karl-mohring/TrafficCounter/Tests/Test 04 - Lidar (overpass)/Data/Traffic Count - Test 4 - 2015.06.02 1617.xlsx

Sheet: RAW
2015-06-02 | 16:17:47 | 694 | - | INFO | - | Incoming | packet: | {u'count_pir': | 0 | u'lidar_range': | 0 | u'of_dy': | 0 | u'count_uvd': | 0 | u'of_dx': | 0 | u'uvd_range': | 621 | u'count_of': | 0 | u'count_lidar': | 0 | u'version': | 4 | u'of_status': | FALSE | u'pir_status': | FALSE | u'id': | u'trafficCount' | u'of_connected': | FALSE
2015-06-02 | 16:17:56 | 720 | - | INFO | - | Incoming | packet: | {u'count_pir': | 0 | u'lidar_range': | 519 | u'of_dy': | 0 | u'count_uvd': | 1 | u'of_dx': | 0 | u'uvd_range': | 336 | u'count_of': | 0 | u'count_lidar': | 0 | u'version': | 4 | u'of_status': | FALSE | u'pir_status': | FALSE | u'id': | u'trafficCount' | u'of_connected': | TRUE
2015-06-02 | 16:17:59 | 309 | - | INFO | - | Incoming | packet: | {u'count_pir': | 0 | u'lidar_range': | 518 | u'of_dy': | 0 | u'count_uvd': | 2 | u'of_dx': | 0 | u'uvd_range': | 522 | u'count_of': | 0 | u'count_lidar': | 0 | u'version': | 4 | u'of_status': | FALSE | u'pir_status': | FALSE | u'id': | u'trafficCount' | u'of_connected': | TRUE
2015-06-02 | 16:18:06 | 519 | - | INFO | - | Incoming | packet: | {u'count_pir': | 0 | u'lidar_range': | 518 | u'of_dy': | 0 | u'count_uvd': | 3 | u'of_dx': | 0 | u'uvd_range': | 427 | u'count_of': | 0 | u'count_lidar': | 0 | u'version': | 4 | u'of_status': | FALSE | u'pir_status': | FALSE | u'id': | u'trafficCount' | u'of_connected': | TRUE
2015-06-02 | 16:18:12 | 332 | - | INFO | - | Incoming | packet: | {u'count_pir': | 0 | u'lidar_range': | 519 | u'of_dy': | 0 | u'count_uvd': | 4 | u'of_dx': | 0 | u'uvd_range': | 338 | u'count_of': | 0 | u'count_lidar': | 0 | u'version': | 4 | u'of_status': | FALSE | u'pir_status': | FALSE | u'id': | u'trafficCount' | u'of_connected': | TRUE
2015-06-02 | 16:18:14 | 318 | - | INFO | - | Incoming | packet: | {u'count_pir': | 0 | u'lidar_range': | 517 | u'of_dy': | 0 | u'count_uvd': | 5 | u'of_dx': | 0 | u'uvd_range': | 292 | u'count_of': | 0 | u'count_lidar': | 0 | u'version': | 4 | u'of_status': | FALSE | u'pir_status': | FALSE | u'id': | u'trafficCount' | u'of_connected': | TRUE
2015-06-02 | 16:18:14 | 917 | - | INFO | - | Incoming | packet: | {u'count_pir': | 0 | u'lidar_range': | 518 | u'of_dy': | 0 | u'count_uvd': | 6 | u'of_dx': | 0 | u'uvd_range': | 553 | u'count_of': | 0 | u'count_lidar': | 0 | u'version': | 4 | u'of_status': | FALSE | u'pir_status': | FALSE | u'id': | u'trafficCount' | u'of_connected': | TRUE
2015-06-02 | 16:18:16 | 318 | - | INFO | - | Incoming | packet: | {u'count_pir': | 0 | u'lidar_range': | 517 | u'of_dy': | 0 | u'count_uvd': | 7 | u'of_dx': | 0 | u'uvd_range': | 407 | u'count_of': | 0 | u'count_lidar': | 0 | u'version': | 4 | u'of_status': | FALSE | u'pir_status': | FALSE | u'id': | u'trafficCount' | u'of_connected': | TRUE
2015-06-02 | 16:18:18 | 341 | - | INFO | - | Incoming | packet: | {u'count_pir': | 0 | u'lidar_range': | 516 | u'of_dy': | 0 | u'count_uvd': | 8 | u'of_dx': | 0 | u'uvd_range': | 483 | u'count_of': | 0 | u'count_lidar': | 0 | u'version': | 4 | u'of_status': | FALSE | u'pir_status': | FALSE | u'id': | u'trafficCount' | u'of_connected': | TRUE
2015-06-02 | 16:18:18 | 720 | - | INFO | - | Incoming | packet: | {u'count_pir': | 0 | u'lidar_range': | 519 | u'of_dy': | 0 | u'count_uvd': | 9 | u'of_dx': | 0 | u'uvd_range': | 500 | u'count_of': | 0 | u'count_lidar': | 0 | u'version': | 4 | u'of_status': | FALSE | u'pir_status': | FALSE | u'id': | u'trafficCount' | u'of_connected': | TRUE
2015-06-02 | 16:18:24 | 512 | - | INFO | - | Incoming | packet: | {u'count_pir': | 0 | u'lidar_range': | 518 | u'of_dy': | 0 | u'count_uvd': | 10 | u'of_dx': | 0 | u'uvd_range': | 382 | u'count_of': | 0 | u'count_lidar': | 0 | u'version': | 4 | u'of_status': | FALSE | u'pir_status': | FALSE | u'id': | u'trafficCount' | u'of_connected': | TRUE
2015-06-02 | 16:18:27 | 903 | - | INFO | - | Incoming | packet: | {u'count_pir': | 0 | u'lidar_range': | 5 | u'of_dy': | 0 | u'count_uvd': | 10 | u'of_dx': | 0 | u'uvd_range': | 622 | u'count_of': | 0 | u'count_lidar': | 1 | u'version': | 4 | u'of_status': | FALSE | u'pir_status': | FALSE | u'id': | u'trafficCount' | u'of_connected': | TRUE
2015-06-02 | 16:18:28 | 907 | - | INFO | - | Incoming | packet: | {u'count_pir': | 1 | u'lidar_range': | 519 | u'of_dy': | 0 | u'count_uvd': | 10 | u'of_dx': | 0 | u'uvd_range': | 622 | u'count_of': | 0 | u'count_lidar': | 1 | u'version': | 4 | u'of_status': | FALSE | u'pir_status': | FALSE | u'id': | u'trafficCount' | u'of_connected': | TRUE
2015-06-02 | 16:18:30 | 306 | - | INFO | - | Incoming | packet: | {u'count_pir': | 1 | u'lidar_range': | 516 | u'of_dy': | 0 | u'count_uvd': | 11 | u'of_dx': | 0 | u'uvd_range': | 389 | u'count_of': | 0 | u'count_lidar': | 1 | u'version': | 4 | u'of_status': | FALSE | u'pir_status': | TRUE | u'id': | u'trafficCount' | u'of_connected': | TRUE
2015-06-02 | 16:18:34 | 305 | - | INFO | - | Incoming | packet: | {u'count_pir': | 1 | u'lidar_range': | 517 | u'of_dy': | 0 | u'count_uvd': | 12 | u'of_dx': | 0 | u'uvd_range': | 520 | u'count_of': | 0 | u'count_lidar': | 1 | u'version': | 4 | u'of_status': | FALSE | u'pir_status': | TRUE | u'id': | u'trafficCount' | u'of_connected': | TRUE
2015-06-02 | 16:18:36 | 305 | - | INFO | - | Incoming | packet: | {u'count_pir': | 1 | u'lidar_range': | 521 | u'of_dy': | 0 | u'count_uvd': | 13 | u'of_dx': | 0 | u'uvd_range': | 536 | u'count_of': | 0 | u'count_lidar': | 1 | u'version': | 4 | u'of_status': | FALSE | u'pir_status': | FALSE | u'id': | u'trafficCount' | u'of_connected': | TRUE
2015-06-02 | 16:18:38 | 107 | - | INFO | - | Incoming | packet: | {u'count_pir': | 1 | u'lidar_range': | 518 | u'of_dy': | 0 | u'count_uvd': | 14 | u'of_dx': | 0 | u'uvd_range': | 284 | u'count_of': | 0 | u'count_lidar': | 1 | u'version': | 4 | u'of_status': | FALSE | u'pir_status': | FALSE | u'id': | u'trafficCount' | u'of_connected': | TRUE
2015-06-02 | 16:18:42 | 506 | - | INFO | - | Incoming | packet: | {u'count_pir': | 1 | u'lidar_range': | 518 | u'of_dy': | 0 | u'count_uvd': | 15 | u'of_dx': | 0 | u'uvd_range': | 556 | u'count_of': | 0 | u'count_lidar': | 1 | u'version': | 4 | u'of_status': | FALSE | u'pir_status': | FALSE | u'id': | u'trafficCount' | u'of_connected': | TRUE
2015-06-02 | 16:18:42 | 934 | - | INFO | - | Incoming | packet: | {u'count_pir': | 2 | u'lidar_range': | 519 | u'of_dy': | 0 | u'count_uvd': | 15 | u'of_dx': | 0 | u'uvd_range': | 622 | u'count_of': | 0 | u'count_lidar': | 1 | u'version': | 4 | u'of_status': | FALSE | u'pir_status': | FALSE | u'id': | u'trafficCount' | u'of_connected': | TRUE
2015-06-02 | 16:18:53 | 706 | - | INFO | - | Incoming | packet: | {u'count_pir': | 2 | u'lidar_range': | 516 | u'of_dy': | 0 | u'count_uvd': | 16 | u'of_dx': | 0 | u'uvd_range': | 490 | u'count_of': | 0 | u'count_lidar': | 1 | u'version': | 4 | u'of_status': | FALSE | u'pir_status': | FALSE | u'id': | u'trafficCount' | u'of_connected': | TRUE
2015-06-02 | 16:19:04 | 505 | - | INFO | - | Incoming | packet: | {u'count_pir': | 2 | u'lidar_range': | 519 | u'of_dy': | 0 | u'count_uvd': | 17 | u'of_dx': | 0 | u'uvd_range': | 370 | u'count_of': | 0 | u'count_lidar': | 1 | u'version': | 4 | u'of_status': | FALSE | u'pir_status': | FALSE | u'id': | u'trafficCount' | u'of_connected': | TRUE
2015-06-02 | 16:19:14 | 506 | - | INFO | - | Incoming | packet: | {u'count_pir': | 2 | u'lidar_range': | 517 | u'of_dy': | 0 | u'count_uvd': | 18 | u'of_dx': | 0 | u'uvd_range': | 294 | u'count_of': | 0 | u'count_lidar': | 1 | u'version': | 4 | u'of_status': | FALSE | u'pir_status': | FALSE | u'id': | u'trafficCount' | u'of_connected': | TRUE
2015-06-02 | 16:19:18 | 506 | - | INFO | - | Incoming | packet: | {u'count_pir': | 2 | u'lidar_range': | 520 | u'of_dy': | 0 | u'count_uvd': | 19 | u'of_dx': | 0 | u'uvd_range': | 275 | u'count_of': | 0 | u'count_lidar': | 1 | u'version': | 4 | u'of_status': | FALSE | u'pir_status': | FALSE | u'id': | u'trafficCount' | u'of_connected': | TRUE
2015-06-02 | 16:19:18 | 907 | - | INFO | - | Incoming | packet: | {u'count_pir': | 2 | u'lidar_range': | 518 | u'of_dy': | 0 | u'count_uvd': | 20 | u'of_dx': | 0 | u'uvd_range': | 552 | u'count_of': | 0 | u'count_lidar': | 1 | u'version': | 4 | u'of_status': | FALSE | u'pir_status': | FALSE | u'id': | u'trafficCount' | u'of_connected': | TRUE
2015-06-02 | 16:19:20 | 905 | - | INFO | - | Incoming | packet: | {u'count_pir': | 2 | u'lidar_range': | 520 | u'of_dy': | 0 | u'count_uvd': | 21 | u'of_dx': | 0 | u'uvd_range': | 519 | u'count_of': | 0 | u'count_lidar': | 1 | u'version': | 4 | u'of_status': | FALSE | u'pir_status': | FALSE | u'id': | u'trafficCount' | u'of_connected': | TRUE
2015-06-02 | 16:19:29 | 505 | - | INFO | - | Incoming | packet: | {u'count_pir': | 2 | u'lidar_range': | 517 | u'of_dy': | 0 | u'count_uvd': | 22 | u'of_dx': | 0 | u'uvd_range': | 487 | u'count_of': | 0 | u'count_lidar': | 1 | u'version': | 4 | u'of_status': | FALSE | u'pir_status': | FALSE | u'id': | u'trafficCount' | u'of_connected': | TRUE
2015-06-02 | 16:19:30 | 706 | - | INFO | - | Incoming | packet: | {u'count_pir': | 2 | u'lidar_range': | 518 | u'of_dy': | 0 | u'count_uvd': | 23 | u'of_dx': | 0 | u'uvd_range': | 501 | u'count_of': | 0 | u'count_lidar': | 1 | u'version': | 4 | u'of_status': | FALSE | u'pir_status': | FALSE | u'id': | u'trafficCount' | u'of_connected': | TRUE
2015-06-02 | 16:19:32 | 505 | - | INFO | - | Incoming | packet: | {u'count_pir': | 2 | u'lidar_range': | 517 | u'of_dy': | 0 | u'count_uvd': | 24 | u'of_dx': | 0 | u'uvd_range': | 464 | u'count_of': | 0 | u'count_lidar': | 1 | u'version': | 4 | u'of_status': | FALSE | u'pir_status': | FALSE | u'id': | u'trafficCount' | u'of_connected': | TRUE
2015-06-02 | 16:19:33 | 706 | - | INFO | - | Incoming | packet: | {u'count_pir': | 2 | u'lidar_range': | 519 | u'of_dy': | 0 | u'count_uvd': | 25 | u'of_dx': | 0 | u'uvd_range': | 352 | u'count_of': | 0 | u'count_lidar': | 1 | u'version': | 4 | u'of_status': | FALSE | u'pir_status': | FALSE | u'id': | u'trafficCount' | u'of_connected': | TRUE
2015-06-02 | 16:19:36 | 904 | - | INFO | - | Incoming | packet: | {u'count_pir': | 2 | u'lidar_range': | 518 | u'of_dy': | 0 | u'count_uvd': | 26 | u'of_dx': | 0 | u'uvd_range': | 434 | u'count_of': | 0 | u'count_lidar': | 1 | u'version': | 4 | u'of_status': | FALSE | u'pir_status': | FALSE | u'id': | u'trafficCount' | u'of_connected': | TRUE
2015-06-02 | 16:19:39 | 706 | - | INFO | - | Incoming | packet: | {u'count_pir': | 2 | u'lidar_range': | 519 | u'of_dy': | 0 | u'count_uvd': | 27 | u'of_dx': | 0 | u'uvd_range': | 305 | u'count_of': | 0 | u'count_lidar': | 1 | u'version': | 4 | u'of_status': | FALSE | u'pir_status': | FALSE | u'id': | u'trafficCount' | u'of_connected': | TRUE
2015-06-02 | 16:19:46 | 105 | - | INFO | - | Incoming | packet: | {u'count_pir': | 2 | u'lidar_range': | 515 | u'of_dy': | 0 | u'count_uvd': | 28 | u'of_dx': | 0 | u'uvd_range': | 568 | u'count_of': | 0 | u'count_lidar': | 1 | u'version': | 4 | u'of_status': | FALSE | u'pir_status': | FALSE | u'id': | u'trafficCount' | u'of_connected': | TRUE
2015-06-02 | 16:19:48 | 506 | - | INFO | - | Incoming | packet: | {u'count_pir': | 2 | u'lidar_range': | 519 | u'of_dy': | 0 | u'count_uvd': | 29 | u'of_dx': | 0 | u'uvd_range': | 301 | u'count_of': | 0 | u'count_lidar': | 1 | u'version': | 4 | u'of_status': | FALSE | u'pir_status': | FALSE | u'id': | u'trafficCount' | u'of_connected': | TRUE
2015-06-02 | 16:19:48 | 905 | - | INFO | - | Incoming | packet: | {u'count_pir': | 2 | u'lidar_range': | 517 | u'of_dy': | 0 | u'count_uvd': | 30 | u'of_dx': | 0 | u'uvd_range': | 291 | u'count_of': | 0 | u'count_lidar': | 1 | u'version': | 4 | u'of_status': | FALSE | u'pir_status': | FALSE | u'id': | u'trafficCount' | u'of_connected': | TRUE
2015-06-02 | 16:19:49 | 506 | - | INFO | - | Incoming | packet: | {u'count_pir': | 2 | u'lidar_range': | 518 | u'of_dy': | 0 | u'count_uvd': | 31 | u'of_dx': | 0 | u'uvd_range': | 549 | u'count_of': | 0 | u'count_lidar': | 1 | u'version': | 4 | u'of_status': | FALSE | u'pir_status': | FALSE | u'id': | u'trafficCount' | u'of_connected': | TRUE
2015-06-02 | 16:19:57 | 704 | - | INFO | - | Incoming | packet: | {u'count_pir': | 2 | u'lidar_range': | 518 | u'of_dy': | 0 | u'count_uvd': | 32 | u'of_dx': | 0 | u'uvd_range': | 457 | u'count_of': | 0 | u'count_lidar': | 1 | u'version': | 4 | u'of_status': | FALSE | u'pir_status': | FALSE | u'id': | u'trafficCount' | u'of_connected': | TRUE
2015-06-02 | 16:19:58 | 904 | - | INFO | - | Incoming | packet: | {u'count_pir': | 2 | u'lidar_range': | 517 | u'of_dy': | 0 | u'count_uvd': | 33 | u'of_dx': | 0 | u'uvd_range': | 390 | u'count_of': | 0 | u'count_lidar': | 1 | u'version': | 4 | u'of_status': | FALSE | u'pir_status': | FALSE | u'id': | u'trafficCount' | u'of_connected': | TRUE
2015-06-02 | 16:20:05 | 101 | - | INFO | - | Incoming | packet: | {u'count_pir': | 2 | u'lidar_range': | 373 | u'of_dy': | 0 | u'count_uvd': | 33 | u'of_dx': | 0 | u'uvd_range': | 621 | u'count_of': | 0 | u'count_lidar': | 2 | u'version': | 4 | u'of_status': | FALSE | u'pir_status': | FALSE | u'id': | u'trafficCount' | u'of_connected': | TRUE
2015-06-02 | 16:20:05 | 506 | - | INFO | - | Incoming | packet: | {u'count_pir': | 2 | u'lidar_range': | 517 | u'of_dy': | 0 | u'count_uvd': | 34 | u'of_dx': | 0 | u'uvd_range': | 545 | u'count_of': | 0 | u'count_lidar': | 2 | u'version': | 4 | u'of_status': | FALSE | u'pir_status': | FALSE | u'id': | u'trafficCount' | u'of_connected': | TRUE
2015-06-02 | 16:20:07 | 305 | - | INFO | - | Incoming | packet: | {u'count_pir': | 2 | u'lidar_range': | 521 | u'of_dy': | 0 | u'count_uvd': | 35 | u'of_dx': | 0 | u'uvd_range': | 369 | u'count_of': | 0 | u'count_lidar': | 2 | u'version': | 4 | u'of_status': | FALSE | u'pir_status': | FALSE | u'id': | u'trafficCount' | u'of_connected': | TRUE
2015-06-02 | 16:20:08 | 904 | - | INFO | - | Incoming | packet: | {u'count_pir': | 2 | u'lidar_range': | 519 | u'of_dy': | 0 | u'count_uvd': | 36 | u'of_dx': | 0 | u'uvd_range': | 399 | u'count_of': | 0 | u'count_lidar': | 2 | u'version': | 4 | u'of_status': | FALSE | u'pir_status': | FALSE | u'id': | u'trafficCount' | u'of_connected': | TRUE
2015-06-02 | 16:20:11 | 305 | - | INFO | - | Incoming | packet: | {u'count_pir': | 2 | u'lidar_range': | 517 | u'of_dy': | 0 | u'count_uvd': | 37 | u'of_dx': | 0 | u'uvd_range': | 350 | u'count_of': | 0 | u'count_lidar': | 2 | u'version': | 4 | u'of_status': | FALSE | u'pir_status': | FALSE | u'id': | u'trafficCount' | u'of_connected': | TRUE
2015-06-02 | 16:20:22 | 904 | - | INFO | - | Incoming | packet: | {u'count_pir': | 2 | u'lidar_range': | 516 | u'of_dy': | 0 | u'count_uvd': | 38 | u'of_dx': | 0 | u'uvd_range': | 432 | u'count_of': | 0 | u'count_lidar': | 2 | u'version': | 4 | u'of_status': | FALSE | u'pir_status': | FALSE | u'id': | u'trafficCount' | u'of_connected': | TRUE
2015-06-02 | 16:20:27 | 966 | - | INFO | - | Incoming | packet: | {u'count_pir': | 3 | u'lidar_range': | 518 | u'of_dy': | 0 | u'count_uvd': | 38 | u'of_dx': | 0 | u'uvd_range': | 621 | u'count_of': | 0 | u'count_lidar': | 2 | u'version': | 4 | u'of_status': | FALSE | u'pir_status': | FALSE | u'id': | u'trafficCount' | u'of_connected': | TRUE
2015-06-02 | 16:20:30 | 704 | - | INFO | - | Incoming | packet: | {u'count_pir': | 3 | u'lidar_range': | 514 | u'of_dy': | 0 | u'count_uvd': | 39 | u'of_dx': | 0 | u'uvd_range': | 554 | u'count_of': | 0 | u'count_lidar': | 2 | u'version': | 4 | u'of_status': | FALSE | u'pir_status': | TRUE | u'id': | u'trafficCount' | u'of_connected': | TRUE
2015-06-02 | 16:20:39 | 904 | - | INFO | - | Incoming | packet: | {u'count_pir': | 3 | u'lidar_range': | 518 | u'of_dy': | 0 | u'count_uvd': | 40 | u'of_dx': | 0 | u'uvd_range': | 335 | u'count_of': | 0 | u'count_lidar': | 2 | u'version': | 4 | u'of_status': | FALSE | u'pir_status': | FALSE | u'id': | u'trafficCount' | u'of_connected': | TRUE
2015-06-02 | 16:20:46 | 305 | - | INFO | - | Incoming | packet: | {u'count_pir': | 3 | u'lidar_range': | 518 | u'of_dy': | 0 | u'count_uvd': | 41 | u'of_dx': | 0 | u'uvd_range': | 566 | u'count_of': | 0 | u'count_lidar': | 2 | u'version': | 4 | u'of_status': | FALSE | u'pir_status': | FALSE | u'id': | u'trafficCount' | u'of_connected': | TRUE
2015-06-02 | 16:20:48 | 105 | - | INFO | - | Incoming | packet: | {u'count_pir': | 3 | u'lidar_range': | 517 | u'of_dy': | 0 | u'count_uvd': | 42 | u'of_dx': | 0 | u'uvd_range': | 375 | u'count_of': | 0 | u'count_lidar': | 2 | u'version': | 4 | u'of_status': | FALSE | u'pir_status': | FALSE | u'id': | u'trafficCount' | u'of_connected': | TRUE
2015-06-02 | 16:20:57 | 911 | - | INFO | - | Incoming | packet: | {u'count_pir': | 3 | u'lidar_range': | 518 | u'of_dy': | 0 | u'count_uvd': | 43 | u'of_dx': | 0 | u'uvd_range': | 467 | u'count_of': | 0 | u'count_lidar': | 2 | u'version': | 4 | u'of_status': | FALSE | u'pir_status': | FALSE | u'id': | u'trafficCount' | u'of_connected': | TRUE
2015-06-02 | 16:21:01 | 706 | - | INFO | - | Incoming | packet: | {u'count_pir': | 3 | u'lidar_range': | 520 | u'of_dy': | 0 | u'count_uvd': | 44 | u'of_dx': | 0 | u'uvd_range': | 484 | u'count_of': | 0 | u'count_lidar': | 2 | u'version': | 4 | u'of_status': | FALSE | u'pir_status': | FALSE | u'id': | u'trafficCount' | u'of_connected': | TRUE
2015-06-02 | 16:21:07 | 506 | - | INFO | - | Incoming | packet: | {u'count_pir': | 3 | u'lidar_range': | 519 | u'of_dy': | 0 | u'count_uvd': | 45 | u'of_dx': | 0 | u'uvd_range': | 502 | u'count_of': | 0 | u'count_lidar': | 2 | u'version': | 4 | u'of_status': | FALSE | u'pir_status': | FALSE | u'id': | u'trafficCount' | u'of_connected': | TRUE
2015-06-02 | 16:21:10 | 915 | - | INFO | - | Incoming | packet: | {u'count_pir': | 3 | u'lidar_range': | 518 | u'of_dy': | 0 | u'count_uvd': | 46 | u'of_dx': | 0 | u'uvd_range': | 332 | u'count_of': | 0 | u'count_lidar': | 2 | u'version': | 4 | u'of_status': | FALSE | u'pir_status': | FALSE | u'id': | u'trafficCount' | u'of_connected': | TRUE
2015-06-02 | 16:21:13 | 312 | - | INFO | - | Incoming | packet: | {u'count_pir': | 3 | u'lidar_range': | 519 | u'of_dy': | 0 | u'count_uvd': | 47 | u'of_dx': | 0 | u'uvd_range': | 495 | u'count_of': | 0 | u'count_lidar': | 2 | u'version': | 4 | u'of_status': | FALSE | u'pir_status': | FALSE | u'id': | u'trafficCount' | u'of_connected': | TRUE
2015-06-02 | 16:21:18 | 302 | - | INFO | - | Incoming | packet: | {u'count_pir': | 3 | u'lidar_range': | 369 | u'of_dy': | 0 | u'count_uvd': | 47 | u'of_dx': | 0 | u'uvd_range': | 622 | u'count_of': | 0 | u'count_lidar': | 3 | u'version': | 4 | u'of_status': | FALSE | u'pir_status': | FALSE | u'id': | u'trafficCount' | u'of_connected': | TRUE
2015-06-02 | 16:21:19 | 706 | - | INFO | - | Incoming | packet: | {u'count_pir': | 3 | u'lidar_range': | 516 | u'of_dy': | 0 | u'count_uvd': | 48 | u'of_dx': | 0 | u'uvd_range': | 444 | u'count_of': | 0 | u'count_lidar': | 3 | u'version': | 4 | u'of_status': | FALSE | u'pir_status': | FALSE | u'id': | u'trafficCount' | u'of_connected': | TRUE
2015-06-02 | 16:21:20 | 305 | - | INFO | - | Incoming | packet: | {u'count_pir': | 3 | u'lidar_range': | 518 | u'of_dy': | 0 | u'count_uvd': | 49 | u'of_dx': | 0 | u'uvd_range': | 553 | u'count_of': | 0 | u'count_lidar': | 3 | u'version': | 4 | u'of_status': | FALSE | u'pir_status': | FALSE | u'id': | u'trafficCount' | u'of_connected': | TRUE
2015-06-02 | 16:21:22 | 506 | - | INFO | - | Incoming | packet: | {u'count_pir': | 3 | u'lidar_range': | 514 | u'of_dy': | 0 | u'count_uvd': | 50 | u'of_dx': | 0 | u'uvd_range': | 266 | u'count_of': | 0 | u'count_lidar': | 3 | u'version': | 4 | u'of_status': | FALSE | u'pir_status': | FALSE | u'id': | u'trafficCount' | u'of_connected': | TRUE
2015-06-02 | 16:21:26 | 505 | - | INFO | - | Incoming | packet: | {u'count_pir': | 3 | u'lidar_range': | 517 | u'of_dy': | 0 | u'count_uvd': | 51 | u'of_dx': | 0 | u'uvd_range': | 404 | u'count_of': | 0 | u'count_lidar': | 3 | u'version': | 4 | u'of_status': | FALSE | u'pir_status': | FALSE | u'id': | u'trafficCount' | u'of_connected': | TRUE
2015-06-02 | 16:21:27 | 701 | - | INFO | - | Incoming | packet: | {u'count_pir': | 3 | u'lidar_range': | 418 | u'of_dy': | 0 | u'count_uvd': | 51 | u'of_dx': | 0 | u'uvd_range': | 622 | u'count_of': | 0 | u'count_lidar': | 4 | u'version': | 4 | u'of_status': | FALSE | u'pir_status': | FALSE | u'id': | u'trafficCount' | u'of_connected': | TRUE
2015-06-02 | 16:21:28 | 904 | - | INFO | - | Incoming | packet: | {u'count_pir': | 3 | u'lidar_range': | 519 | u'of_dy': | 0 | u'count_uvd': | 52 | u'of_dx': | 0 | u'uvd_range': | 513 | u'count_of': | 0 | u'count_lidar': | 4 | u'version': | 4 | u'of_status': | FALSE | u'pir_status': | FALSE | u'id': | u'trafficCount' | u'of_connected': | TRUE
2015-06-02 | 16:21:30 | 305 | - | INFO | - | Incoming | packet: | {u'count_pir': | 3 | u'lidar_range': | 519 | u'of_dy': | 0 | u'count_uvd': | 53 | u'of_dx': | 0 | u'uvd_range': | 380 | u'count_of': | 0 | u'count_lidar': | 4 | u'version': | 4 | u'of_status': | FALSE | u'pir_status': | FALSE | u'id': | u'trafficCount' | u'of_connected': | TRUE
2015-06-02 | 16:21:32 | 707 | - | INFO | - | Incoming | packet: | {u'count_pir': | 3 | u'lidar_range': | 521 | u'of_dy': | 0 | u'count_uvd': | 54 | u'of_dx': | 0 | u'uvd_range': | 480 | u'count_of': | 0 | u'count_lidar': | 4 | u'version': | 4 | u'of_status': | FALSE | u'pir_status': | FALSE | u'id': | u'trafficCount' | u'of_connected': | TRUE
2015-06-02 | 16:21:36 | 105 | - | INFO | - | Incoming | packet: | {u'count_pir': | 3 | u'lidar_range': | 518 | u'of_dy': | 0 | u'count_uvd': | 55 | u'of_dx': | 0 | u'uvd_range': | 362 | u'count_of': | 0 | u'count_lidar': | 4 | u'version': | 4 | u'of_status': | FALSE | u'pir_status': | FALSE | u'id': | u'trafficCount' | u'of_connected': | TRUE
2015-06-02 | 16:21:41 | 904 | - | INFO | - | Incoming | packet: | {u'count_pir': | 3 | u'lidar_range': | 518 | u'of_dy': | 0 | u'count_uvd': | 56 | u'of_dx': | 0 | u'uvd_range': | 331 | u'count_of': | 0 | u'count_lidar': | 4 | u'version': | 4 | u'of_status': | FALSE | u'pir_status': | FALSE | u'id': | u'trafficCount' | u'of_connected': | TRUE
2015-06-02 | 16:21:43 | 904 | - | INFO | - | Incoming | packet: | {u'count_pir': | 3 | u'lidar_range': | 519 | u'of_dy': | 0 | u'count_uvd': | 57 | u'of_dx': | 0 | u'uvd_range': | 422 | u'count_of': | 0 | u'count_lidar': | 4 | u'version': | 4 | u'of_status': | FALSE | u'pir_status': | FALSE | u'id': | u'trafficCount' | u'of_connected': | TRUE
2015-06-02 | 16:21:44 | 500 | - | INFO | - | Incoming | packet: | {u'count_pir': | 3 | u'lidar_range': | 341 | u'of_dy': | 0 | u'count_uvd': | 57 | u'of_dx': | 0 | u'uvd_range': | 621 | u'count_of': | 0 | u'count_lidar': | 5 | u'version': | 4 | u'of_status': | FALSE | u'pir_status': | FALSE | u'id': | u'trafficCount' | u'of_connected': | TRUE
2015-06-02 | 16:21:45 | 303 | - | INFO | - | Incoming | packet: | {u'count_pir': | 3 | u'lidar_range': | 519 | u'of_dy': | 0 | u'count_uvd': | 58 | u'of_dx': | 0 | u'uvd_range': | 334 | u'count_of': | 0 | u'count_lidar': | 5 | u'version': | 4 | u'of_status': | FALSE | u'pir_status': | FALSE | u'id': | u'trafficCount' | u'of_connected': | TRUE
2015-06-02 | 16:21:46 | 99 | - | INFO | - | Incoming | packet: | {u'count_pir': | 3 | u'lidar_range': | 413 | u'of_dy': | 0 | u'count_uvd': | 58 | u'of_dx': | 0 | u'uvd_range': | 622 | u'count_of': | 0 | u'count_lidar': | 6 | u'version': | 4 | u'of_status': | FALSE | u'pir_status': | FALSE | u'id': | u'trafficCount' | u'of_connected': | TRUE
2015-06-02 | 16:21:47 | 704 | - | INFO | - | Incoming | packet: | {u'count_pir': | 3 | u'lidar_range': | 490 | u'of_dy': | 0 | u'count_uvd': | 59 | u'of_dx': | 0 | u'uvd_range': | 298 | u'count_of': | 0 | u'count_lidar': | 6 | u'version': | 4 | u'of_status': | FALSE | u'pir_status': | FALSE | u'id': | u'trafficCount' | u'of_connected': | TRUE
2015-06-02 | 16:21:48 | 500 | - | INFO | - | Incoming | packet: | {u'count_pir': | 3 | u'lidar_range': | 402 | u'of_dy': | 0 | u'count_uvd': | 59 | u'of_dx': | 0 | u'uvd_range': | 585 | u'count_of': | 0 | u'count_lidar': | 7 | u'version': | 4 | u'of_status': | FALSE | u'pir_status': | FALSE | u'id': | u'trafficCount' | u'of_connected': | TRUE
2015-06-02 | 16:21:50 | 305 | - | INFO | - | Incoming | packet: | {u'count_pir': | 3 | u'lidar_range': | 520 | u'of_dy': | 0 | u'count_uvd': | 60 | u'of_dx': | 0 | u'uvd_range': | 570 | u'count_of': | 0 | u'count_lidar': | 7 | u'version': | 4 | u'of_status': | FALSE | u'pir_status': | FALSE | u'id': | u'trafficCount' | u'of_connected': | TRUE
2015-06-02 | 16:21:51 | 503 | - | INFO | - | Incoming | packet: | {u'count_pir': | 3 | u'lidar_range': | 517 | u'of_dy': | 0 | u'count_uvd': | 61 | u'of_dx': | 0 | u'uvd_range': | 331 | u'count_of': | 0 | u'count_lidar': | 7 | u'version': | 4 | u'of_status': | FALSE | u'pir_status': | FALSE | u'id': | u'trafficCount' | u'of_connected': | TRUE
2015-06-02 | 16:21:55 | 901 | - | INFO | - | Incoming | packet: | {u'count_pir': | 3 | u'lidar_range': | 353 | u'of_dy': | 0 | u'count_uvd': | 61 | u'of_dx': | 0 | u'uvd_range': | 622 | u'count_of': | 0 | u'count_lidar': | 8 | u'version': | 4 | u'of_status': | FALSE | u'pir_status': | FALSE | u'id': | u'trafficCount' | u'of_connected': | TRUE
2015-06-02 | 16:21:57 | 303 | - | INFO | - | Incoming | packet: | {u'count_pir': | 3 | u'lidar_range': | 518 | u'of_dy': | 0 | u'count_uvd': | 62 | u'of_dx': | 0 | u'uvd_range': | 311 | u'count_of': | 0 | u'count_lidar': | 8 | u'version': | 4 | u'of_status': | FALSE | u'pir_status': | FALSE | u'id': | u'trafficCount' | u'of_connected': | TRUE
2015-06-02 | 16:21:57 | 500 | - | INFO | - | Incoming | packet: | {u'count_pir': | 3 | u'lidar_range': | 454 | u'of_dy': | 0 | u'count_uvd': | 62 | u'of_dx': | 0 | u'uvd_range': | 311 | u'count_of': | 0 | u'count_lidar': | 9 | u'version': | 4 | u'of_status': | FALSE | u'pir_status': | FALSE | u'id': | u'trafficCount' | u'of_connected': | TRUE
2015-06-02 | 16:21:58 | 503 | - | INFO | - | Incoming | packet: | {u'count_pir': | 3 | u'lidar_range': | 383 | u'of_dy': | 0 | u'count_uvd': | 62 | u'of_dx': | 0 | u'uvd_range': | 621 | u'count_of': | 0 | u'count_lidar': | 10 | u'version': | 4 | u'of_status': | FALSE | u'pir_status': | FALSE | u'id': | u'trafficCount' | u'of_connected': | TRUE
2015-06-02 | 16:22:07 | 105 | - | INFO | - | Incoming | packet: | {u'count_pir': | 3 | u'lidar_range': | 516 | u'of_dy': | 0 | u'count_uvd': | 63 | u'of_dx': | 0 | u'uvd_range': | 431 | u'count_of': | 0 | u'count_lidar': | 10 | u'version': | 4 | u'of_status': | FALSE | u'pir_status': | FALSE | u'id': | u'trafficCount' | u'of_connected': | TRUE
2015-06-02 | 16:22:10 | 0 | - | INFO | - | Incoming | packet: | {u'count_pir': | 4 | u'lidar_range': | 516 | u'of_dy': | 0 | u'count_uvd': | 63 | u'of_dx': | 0 | u'uvd_range': | 622 | u'count_of': | 0 | u'count_lidar': | 10 | u'version': | 4 | u'of_status': | FALSE | u'pir_status': | FALSE | u'id': | u'trafficCount' | u'of_connected': | TRUE
2015-06-02 | 16:22:15 | 104 | - | INFO | - | Incoming | packet: | {u'count_pir': | 4 | u'lidar_range': | 448 | u'of_dy': | 0 | u'count_uvd': | 63 | u'of_dx': | 0 | u'uvd_range': | 622 | u'count_of': | 0 | u'count_lidar': | 11 | u'version': | 4 | u'of_status': | FALSE | u'pir_status': | TRUE | u'id': | u'trafficCount' | u'of_connected': | TRUE
2015-06-02 | 16:22:15 | 302 | - | INFO | - | Incoming | packet: | {u'count_pir': | 4 | u'lidar_range': | 343 | u'of_dy': | 0 | u'count_uvd': | 63 | u'of_dx': | 0 | u'uvd_range': | 621 | u'count_of': | 0 | u'count_lidar': | 12 | u'version': | 4 | u'of_status': | FALSE | u'pir_status': | TRUE | u'id': | u'trafficCount' | u'of_connected': | TRUE
2015-06-02 | 16:22:16 | 305 | - | INFO | - | Incoming | packet: | {u'count_pir': | 4 | u'lidar_range': | 401 | u'of_dy': | 0 | u'count_uvd': | 64 | u'of_dx': | 0 | u'uvd_range': | 290 | u'count_of': | 0 | u'count_lidar': | 12 | u'version': | 4 | u'of_status': | FALSE | u'pir_status': | FALSE | u'id': | u'trafficCount' | u'of_connected': | TRUE
2015-06-02 | 16:22:18 | 704 | - | INFO | - | Incoming | packet: | {u'count_pir': | 4 | u'lidar_range': | 373 | u'of_dy': | 0 | u'count_uvd': | 65 | u'of_dx': | 0 | u'uvd_range': | 401 | u'count_of': | 0 | u'count_lidar': | 12 | u'version': | 4 | u'of_status': | FALSE | u'pir_status': | FALSE | u'id': | u'trafficCount' | u'of_connected': | TRUE
2015-06-02 | 16:22:21 | 703 | - | INFO | - | Incoming | packet: | {u'count_pir': | 4 | u'lidar_range': | 517 | u'of_dy': | 0 | u'count_uvd': | 66 | u'of_dx': | 0 | u'uvd_range': | 429 | u'count_of': | 0 | u'count_lidar': | 12 | u'version': | 4 | u'of_status': | FALSE | u'pir_status': | FALSE | u'id': | u'trafficCount' | u'of_connected': | TRUE
2015-06-02 | 16:22:22 | 704 | - | INFO | - | Incoming | packet: | {u'count_pir': | 4 | u'lidar_range': | 516 | u'of_dy': | 0 | u'count_uvd': | 67 | u'of_dx': | 0 | u'uvd_range': | 513 | u'count_of': | 0 | u'count_lidar': | 12 | u'version': | 4 | u'of_status': | FALSE | u'pir_status': | FALSE | u'id': | u'trafficCount' | u'of_connected': | TRUE
2015-06-02 | 16:22:28 | 505 | - | INFO | - | Incoming | packet: | {u'count_pir': | 4 | u'lidar_range': | 518 | u'of_dy': | 0 | u'count_uvd': | 68 | u'of_dx': | 0 | u'uvd_range': | 475 | u'count_of': | 0 | u'count_lidar': | 12 | u'version': | 4 | u'of_status': | FALSE | u'pir_status': | FALSE | u'id': | u'trafficCount' | u'of_connected': | TRUE
2015-06-02 | 16:22:31 | 904 | - | INFO | - | Incoming | packet: | {u'count_pir': | 4 | u'lidar_range': | 518 | u'of_dy': | 0 | u'count_uvd': | 69 | u'of_dx': | 0 | u'uvd_range': | 384 | u'count_of': | 0 | u'count_lidar': | 12 | u'version': | 4 | u'of_status': | FALSE | u'pir_status': | FALSE | u'id': | u'trafficCount' | u'of_connected': | TRUE
2015-06-02 | 16:22:35 | 704 | - | INFO | - | Incoming | packet: | {u'count_pir': | 4 | u'lidar_range': | 521 | u'of_dy': | 0 | u'count_uvd': | 70 | u'of_dx': | 0 | u'uvd_range': | 273 | u'count_of': | 0 | u'count_lidar': | 12 | u'version': | 4 | u'of_status': | FALSE | u'pir_status': | FALSE | u'id': | u'trafficCount' | u'of_connected': | TRUE
2015-06-02 | 16:22:38 | 305 | - | INFO | - | Incoming | packet: | {u'count_pir': | 4 | u'lidar_range': | 517 | u'of_dy': | 0 | u'count_uvd': | 71 | u'of_dx': | 0 | u'uvd_range': | 542 | u'count_of': | 0 | u'count_lidar': | 12 | u'version': | 4 | u'of_status': | FALSE | u'pir_status': | FALSE | u'id': | u'trafficCount' | u'of_connected': | TRUE
2015-06-02 | 16:22:49 | 703 | - | INFO | - | Incoming | packet: | {u'count_pir': | 4 | u'lidar_range': | 518 | u'of_dy': | 0 | u'count_uvd': | 72 | u'of_dx': | 0 | u'uvd_range': | 323 | u'count_of': | 0 | u'count_lidar': | 12 | u'version': | 4 | u'of_status': | FALSE | u'pir_status': | FALSE | u'id': | u'trafficCount' | u'of_connected': | TRUE
2015-06-02 | 16:22:51 | 305 | - | INFO | - | Incoming | packet: | {u'count_pir': | 4 | u'lidar_range': | 518 | u'of_dy': | 0 | u'count_uvd': | 73 | u'of_dx': | 0 | u'uvd_range': | 346 | u'count_of': | 0 | u'count_lidar': | 12 | u'version': | 4 | u'of_status': | FALSE | u'pir_status': | FALSE | u'id': | u'trafficCount' | u'of_connected': | TRUE
2015-06-02 | 16:22:53 | 704 | - | INFO | - | Incoming | packet: | {u'count_pir': | 4 | u'lidar_range': | 515 | u'of_dy': | 0 | u'count_uvd': | 74 | u'of_dx': | 0 | u'uvd_range': | 475 | u'count_of': | 0 | u'count_lidar': | 12 | u'version': | 4 | u'of_status': | FALSE | u'pir_status': | FALSE | u'id': | u'trafficCount' | u'of_connected': | TRUE
2015-06-02 | 16:22:59 | 905 | - | INFO | - | Incoming | packet: | {u'count_pir': | 4 | u'lidar_range': | 516 | u'of_dy': | 0 | u'count_uvd': | 75 | u'of_dx': | 0 | u'uvd_range': | 491 | u'count_of': | 0 | u'count_lidar': | 12 | u'version': | 4 | u'of_status': | FALSE | u'pir_status': | FALSE | u'id': | u'trafficCount' | u'of_connected': | TRUE
2015-06-02 | 16:23:16 | 505 | - | INFO | - | Incoming | packet: | {u'count_pir': | 4 | u'lidar_range': | 517 | u'of_dy': | 0 | u'count_uvd': | 76 | u'of_dx': | 0 | u'uvd_range': | 376 | u'count_of': | 0 | u'count_lidar': | 12 | u'version': | 4 | u'of_status': | FALSE | u'pir_status': | FALSE | u'id': | u'trafficCount' | u'of_connected': | TRUE
2015-06-02 | 16:23:20 | 904 | - | INFO | - | Incoming | packet: | {u'count_pir': | 4 | u'lidar_range': | 517 | u'of_dy': | 0 | u'count_uvd': | 77 | u'of_dx': | 0 | u'uvd_range': | 538 | u'count_of': | 0 | u'count_lidar': | 12 | u'version': | 4 | u'of_status': | FALSE | u'pir_status': | FALSE | u'id': | u'trafficCount' | u'of_connected': | TRUE
2015-06-02 | 16:23:30 | 505 | - | INFO | - | Incoming | packet: | {u'count_pir': | 4 | u'lidar_range': | 519 | u'of_dy': | 0 | u'count_uvd': | 78 | u'of_dx': | 0 | u'uvd_range': | 559 | u'count_of': | 0 | u'count_lidar': | 12 | u'version': | 4 | u'of_status': | FALSE | u'pir_status': | FALSE | u'id': | u'trafficCount' | u'of_connected': | TRUE
2015-06-02 | 16:23:31 | 505 | - | INFO | - | Incoming | packet: | {u'count_pir': | 4 | u'lidar_range': | 515 | u'of_dy': | 0 | u'count_uvd': | 79 | u'of_dx': | 0 | u'uvd_range': | 557 | u'count_of': | 0 | u'count_lidar': | 12 | u'version': | 4 | u'of_status': | FALSE | u'pir_status': | FALSE | u'id': | u'trafficCount' | u'of_connected': | TRUE
2015-06-02 | 16:23:33 | 904 | - | INFO | - | Incoming | packet: | {u'count_pir': | 4 | u'lidar_range': | 516 | u'of_dy': | 0 | u'count_uvd': | 80 | u'of_dx': | 0 | u'uvd_range': | 289 | u'count_of': | 0 | u'count_lidar': | 12 | u'version': | 4 | u'of_status': | FALSE | u'pir_status': | FALSE | u'id': | u'trafficCount' | u'of_connected': | TRUE
2015-06-02 | 16:23:36 | 703 | - | INFO | - | Incoming | packet: | {u'count_pir': | 4 | u'lidar_range': | 521 | u'of_dy': | 0 | u'count_uvd': | 81 | u'of_dx': | 0 | u'uvd_range': | 321 | u'count_of': | 0 | u'count_lidar': | 12 | u'version': | 4 | u'of_status': | FALSE | u'pir_status': | FALSE | u'id': | u'trafficCount' | u'of_connected': | TRUE
2015-06-02 | 16:23:37 | 704 | - | INFO | - | Incoming | packet: | {u'count_pir': | 4 | u'lidar_range': | 518 | u'of_dy': | 0 | u'count_uvd': | 82 | u'of_dx': | 0 | u'uvd_range': | 312 | u'count_of': | 0 | u'count_lidar': | 12 | u'version': | 4 | u'of_status': | FALSE | u'pir_status': | FALSE | u'id': | u'trafficCount' | u'of_connected': | TRUE
2015-06-02 | 16:23:41 | 703 | - | INFO | - | Incoming | packet: | {u'count_pir': | 4 | u'lidar_range': | 518 | u'of_dy': | 0 | u'count_uvd': | 83 | u'of_dx': | 0 | u'uvd_range': | 454 | u'count_of': | 0 | u'count_lidar': | 12 | u'version': | 4 | u'of_status': | FALSE | u'pir_status': | FALSE | u'id': | u'trafficCount' | u'of_connected': | TRUE
2015-06-02 | 16:23:46 | 105 | - | INFO | - | Incoming | packet: | {u'count_pir': | 4 | u'lidar_range': | 517 | u'of_dy': | 0 | u'count_uvd': | 84 | u'of_dx': | 0 | u'uvd_range': | 533 | u'count_of': | 0 | u'count_lidar': | 12 | u'version': | 4 | u'of_status': | FALSE | u'pir_status': | FALSE | u'id': | u'trafficCount' | u'of_connected': | TRUE
2015-06-02 | 16:23:49 | 904 | - | INFO | - | Incoming | packet: | {u'count_pir': | 4 | u'lidar_range': | 517 | u'of_dy': | 0 | u'count_uvd': | 85 | u'of_dx': | 0 | u'uvd_range': | 558 | u'count_of': | 0 | u'count_lidar': | 12 | u'version': | 4 | u'of_status': | FALSE | u'pir_status': | FALSE | u'id': | u'trafficCount' | u'of_connected': | TRUE
2015-06-02 | 16:23:56 | 904 | - | INFO | - | Incoming | packet: | {u'count_pir': | 4 | u'lidar_range': | 519 | u'of_dy': | 0 | u'count_uvd': | 86 | u'of_dx': | 0 | u'uvd_range': | 442 | u'count_of': | 0 | u'count_lidar': | 12 | u'version': | 4 | u'of_status': | FALSE | u'pir_status': | FALSE | u'id': | u'trafficCount' | u'of_connected': | TRUE
2015-06-02 | 16:23:58 | 901 | - | INFO | - | Incoming | packet: | {u'count_pir': | 4 | u'lidar_range': | 391 | u'of_dy': | 0 | u'count_uvd': | 86 | u'of_dx': | 0 | u'uvd_range': | 621 | u'count_of': | 0 | u'count_lidar': | 13 | u'version': | 4 | u'of_status': | FALSE | u'pir_status': | FALSE | u'id': | u'trafficCount' | u'of_connected': | TRUE
2015-06-02 | 16:24:01 | 900 | - | INFO | - | Incoming | packet: | {u'count_pir': | 4 | u'lidar_range': | 432 | u'of_dy': | 0 | u'count_uvd': | 86 | u'of_dx': | 0 | u'uvd_range': | 621 | u'count_of': | 0 | u'count_lidar': | 14 | u'version': | 4 | u'of_status': | FALSE | u'pir_status': | FALSE | u'id': | u'trafficCount' | u'of_connected': | TRUE
2015-06-02 | 16:24:08 | 303 | - | INFO | - | Incoming | packet: | {u'count_pir': | 4 | u'lidar_range': | 520 | u'of_dy': | 0 | u'count_uvd': | 87 | u'of_dx': | 0 | u'uvd_range': | 335 | u'count_of': | 0 | u'count_lidar': | 14 | u'version': | 4 | u'of_status': | FALSE | u'pir_status': | FALSE | u'id': | u'trafficCount' | u'of_connected': | TRUE
2015-06-02 | 16:24:08 | 703 | - | INFO | - | Incoming | packet: | {u'count_pir': | 4 | u'lidar_range': | 506 | u'of_dy': | 0 | u'count_uvd': | 88 | u'of_dx': | 0 | u'uvd_range': | 302 | u'count_of': | 0 | u'count_lidar': | 14 | u'version': | 4 | u'of_status': | FALSE | u'pir_status': | FALSE | u'id': | u'trafficCount' | u'of_connected': | TRUE
2015-06-02 | 16:24:09 | 301 | - | INFO | - | Incoming | packet: | {u'count_pir': | 4 | u'lidar_range': | 391 | u'of_dy': | 0 | u'count_uvd': | 88 | u'of_dx': | 0 | u'uvd_range': | 622 | u'count_of': | 0 | u'count_lidar': | 15 | u'version': | 4 | u'of_status': | FALSE | u'pir_status': | FALSE | u'id': | u'trafficCount' | u'of_connected': | TRUE
2015-06-02 | 16:24:10 | 901 | - | INFO | - | Incoming | packet: | {u'count_pir': | 4 | u'lidar_range': | 390 | u'of_dy': | 0 | u'count_uvd': | 88 | u'of_dx': | 0 | u'uvd_range': | 621 | u'count_of': | 0 | u'count_lidar': | 16 | u'version': | 4 | u'of_status': | FALSE | u'pir_status': | FALSE | u'id': | u'trafficCount' | u'of_connected': | TRUE
2015-06-02 | 16:24:12 | 104 | - | INFO | - | Incoming | packet: | {u'count_pir': | 4 | u'lidar_range': | 412 | u'of_dy': | 0 | u'count_uvd': | 89 | u'of_dx': | 0 | u'uvd_range': | 301 | u'count_of': | 0 | u'count_lidar': | 16 | u'version': | 4 | u'of_status': | FALSE | u'pir_status': | FALSE | u'id': | u'trafficCount' | u'of_connected': | TRUE
2015-06-02 | 16:24:14 | 104 | - | INFO | - | Incoming | packet: | {u'count_pir': | 4 | u'lidar_range': | 518 | u'of_dy': | 0 | u'count_uvd': | 90 | u'of_dx': | 0 | u'uvd_range': | 291 | u'count_of': | 0 | u'count_lidar': | 16 | u'version': | 4 | u'of_status': | FALSE | u'pir_status': | FALSE | u'id': | u'trafficCount' | u'of_connected': | TRUE
2015-06-02 | 16:24:22 | 503 | - | INFO | - | Incoming | packet: | {u'count_pir': | 4 | u'lidar_range': | 519 | u'of_dy': | 0 | u'count_uvd': | 91 | u'of_dx': | 0 | u'uvd_range': | 347 | u'count_of': | 0 | u'count_lidar': | 16 | u'version': | 4 | u'of_status': | FALSE | u'pir_status': | FALSE | u'id': | u'trafficCount' | u'of_connected': | TRUE
2015-06-02 | 16:24:23 | 701 | - | INFO | - | Incoming | packet: | {u'count_pir': | 4 | u'lidar_range': | 368 | u'of_dy': | 0 | u'count_uvd': | 91 | u'of_dx': | 0 | u'uvd_range': | 622 | u'count_of': | 0 | u'count_lidar': | 17 | u'version': | 4 | u'of_status': | FALSE | u'pir_status': | FALSE | u'id': | u'trafficCount' | u'of_connected': | TRUE
2015-06-02 | 16:24:27 | 703 | - | INFO | - | Incoming | packet: | {u'count_pir': | 4 | u'lidar_range': | 515 | u'of_dy': | 0 | u'count_uvd': | 92 | u'of_dx': | 0 | u'uvd_range': | 312 | u'count_of': | 0 | u'count_lidar': | 17 | u'version': | 4 | u'of_status': | FALSE | u'pir_status': | FALSE | u'id': | u'trafficCount' | u'of_connected': | TRUE
2015-06-02 | 16:24:30 | 104 | - | INFO | - | Incoming | packet: | {u'count_pir': | 4 | u'lidar_range': | 518 | u'of_dy': | 0 | u'count_uvd': | 93 | u'of_dx': | 0 | u'uvd_range': | 461 | u'count_of': | 0 | u'count_lidar': | 17 | u'version': | 4 | u'of_status': | FALSE | u'pir_status': | FALSE | u'id': | u'trafficCount' | u'of_connected': | TRUE
2015-06-02 | 16:24:37 | 303 | - | INFO | - | Incoming | packet: | {u'count_pir': | 4 | u'lidar_range': | 516 | u'of_dy': | 0 | u'count_uvd': | 94 | u'of_dx': | 0 | u'uvd_range': | 317 | u'count_of': | 0 | u'count_lidar': | 17 | u'version': | 4 | u'of_status': | FALSE | u'pir_status': | FALSE | u'id': | u'trafficCount' | u'of_connected': | TRUE
2015-06-02 | 16:24:39 | 303 | - | INFO | - | Incoming | packet: | {u'count_pir': | 4 | u'lidar_range': | 517 | u'of_dy': | 0 | u'count_uvd': | 95 | u'of_dx': | 0 | u'uvd_range': | 272 | u'count_of': | 0 | u'count_lidar': | 17 | u'version': | 4 | u'of_status': | FALSE | u'pir_status': | FALSE | u'id': | u'trafficCount' | u'of_connected': | TRUE
2015-06-02 | 16:24:39 | 903 | - | INFO | - | Incoming | packet: | {u'count_pir': | 4 | u'lidar_range': | 519 | u'of_dy': | 0 | u'count_uvd': | 96 | u'of_dx': | 0 | u'uvd_range': | 559 | u'count_of': | 0 | u'count_lidar': | 17 | u'version': | 4 | u'of_status': | FALSE | u'pir_status': | FALSE | u'id': | u'trafficCount' | u'of_connected': | TRUE
2015-06-02 | 16:24:42 | 32 | - | INFO | - | Incoming | packet: | {u'count_pir': | 5 | u'lidar_range': | 516 | u'of_dy': | 0 | u'count_uvd': | 96 | u'of_dx': | 0 | u'uvd_range': | 622 | u'count_of': | 0 | u'count_lidar': | 17 | u'version': | 4 | u'of_status': | FALSE | u'pir_status': | FALSE | u'id': | u'trafficCount' | u'of_connected': | TRUE
2015-06-02 | 16:24:43 | 302 | - | INFO | - | Incoming | packet: | {u'count_pir': | 5 | u'lidar_range': | 518 | u'of_dy': | 0 | u'count_uvd': | 97 | u'of_dx': | 0 | u'uvd_range': | 541 | u'count_of': | 0 | u'count_lidar': | 17 | u'version': | 4 | u'of_status': | FALSE | u'pir_status': | TRUE | u'id': | u'trafficCount' | u'of_connected': | TRUE
2015-06-02 | 16:24:47 | 104 | - | INFO | - | Incoming | packet: | {u'count_pir': | 5 | u'lidar_range': | 517 | u'of_dy': | 0 | u'count_uvd': | 98 | u'of_dx': | 0 | u'uvd_range': | 458 | u'count_of': | 0 | u'count_lidar': | 17 | u'version': | 4 | u'of_status': | FALSE | u'pir_status': | TRUE | u'id': | u'trafficCount' | u'of_connected': | TRUE
2015-06-02 | 16:24:50 | 503 | - | INFO | - | Incoming | packet: | {u'count_pir': | 5 | u'lidar_range': | 516 | u'of_dy': | 0 | u'count_uvd': | 99 | u'of_dx': | 0 | u'uvd_range': | 287 | u'count_of': | 0 | u'count_lidar': | 17 | u'version': | 4 | u'of_status': | FALSE | u'pir_status': | FALSE | u'id': | u'trafficCount' | u'of_connected': | TRUE
2015-06-02 | 16:24:55 | 904 | - | INFO | - | Incoming | packet: | {u'count_pir': | 5 | u'lidar_range': | 516 | u'of_dy': | 0 | u'count_uvd': | 100 | u'of_dx': | 0 | u'uvd_range': | 545 | u'count_of': | 0 | u'count_lidar': | 17 | u'version': | 4 | u'of_status': | FALSE | u'pir_status': | FALSE | u'id': | u'trafficCount' | u'of_connected': | TRUE
2015-06-02 | 16:24:58 | 704 | - | INFO | - | Incoming | packet: | {u'count_pir': | 5 | u'lidar_range': | 519 | u'of_dy': | 0 | u'count_uvd': | 101 | u'of_dx': | 0 | u'uvd_range': | 347 | u'count_of': | 0 | u'count_lidar': | 17 | u'version': | 4 | u'of_status': | FALSE | u'pir_status': | FALSE | u'id': | u'trafficCount' | u'of_connected': | TRUE
2015-06-02 | 16:25:01 | 102 | - | INFO | - | Incoming | packet: | {u'count_pir': | 5 | u'lidar_range': | 518 | u'of_dy': | 0 | u'count_uvd': | 102 | u'of_dx': | 0 | u'uvd_range': | 525 | u'count_of': | 0 | u'count_lidar': | 17 | u'version': | 4 | u'of_status': | FALSE | u'pir_status': | FALSE | u'id': | u'trafficCount' | u'of_connected': | TRUE
2015-06-02 | 16:25:13 | 704 | - | INFO | - | Incoming | packet: | {u'count_pir': | 5 | u'lidar_range': | 516 | u'of_dy': | 0 | u'count_uvd': | 103 | u'of_dx': | 0 | u'uvd_range': | 302 | u'count_of': | 0 | u'count_lidar': | 17 | u'version': | 4 | u'of_status': | FALSE | u'pir_status': | FALSE | u'id': | u'trafficCount' | u'of_connected': | TRUE
2015-06-02 | 16:25:19 | 904 | - | INFO | - | Incoming | packet: | {u'count_pir': | 5 | u'lidar_range': | 516 | u'of_dy': | 0 | u'count_uvd': | 104 | u'of_dx': | 0 | u'uvd_range': | 570 | u'count_of': | 0 | u'count_lidar': | 17 | u'version': | 4 | u'of_status': | FALSE | u'pir_status': | FALSE | u'id': | u'trafficCount' | u'of_connected': | TRUE
2015-06-02 | 16:25:20 | 104 | - | INFO | - | Incoming | packet: | {u'count_pir': | 5 | u'lidar_range': | 517 | u'of_dy': | 0 | u'count_uvd': | 105 | u'of_dx': | 0 | u'uvd_range': | 485 | u'count_of': | 0 | u'count_lidar': | 17 | u'version': | 4 | u'of_status': | FALSE | u'pir_status': | FALSE | u'id': | u'trafficCount' | u'of_connected': | TRUE
2015-06-02 | 16:25:24 | 703 | - | INFO | - | Incoming | packet: | {u'count_pir': | 5 | u'lidar_range': | 516 | u'of_dy': | 0 | u'count_uvd': | 106 | u'of_dx': | 0 | u'uvd_range': | 462 | u'count_of': | 0 | u'count_lidar': | 17 | u'version': | 4 | u'of_status': | FALSE | u'pir_status': | FALSE | u'id': | u'trafficCount' | u'of_connected': | TRUE
2015-06-02 | 16:25:29 | 703 | - | INFO | - | Incoming | packet: | {u'count_pir': | 5 | u'lidar_range': | 517 | u'of_dy': | 0 | u'count_uvd': | 107 | u'of_dx': | 0 | u'uvd_range': | 519 | u'count_of': | 0 | u'count_lidar': | 17 | u'version': | 4 | u'of_status': | FALSE | u'pir_status': | FALSE | u'id': | u'trafficCount' | u'of_connected': | TRUE
2015-06-02 | 16:25:35 | 512 | - | INFO | - | Incoming | packet: | {u'count_pir': | 5 | u'lidar_range': | 520 | u'of_dy': | 0 | u'count_uvd': | 108 | u'of_dx': | 0 | u'uvd_range': | 498 | u'count_of': | 0 | u'count_lidar': | 17 | u'version': | 4 | u'of_status': | FALSE | u'pir_status': | FALSE | u'id': | u'trafficCount' | u'of_connected': | TRUE
2015-06-02 | 16:25:39 | 901 | - | INFO | - | Incoming | packet: | {u'count_pir': | 5 | u'lidar_range': | 458 | u'of_dy': | 0 | u'count_uvd': | 108 | u'of_dx': | 0 | u'uvd_range': | 621 | u'count_of': | 0 | u'count_lidar': | 18 | u'version': | 4 | u'of_status': | FALSE | u'pir_status': | FALSE | u'id': | u'trafficCount' | u'of_connected': | TRUE
2015-06-02 | 16:25:46 | 704 | - | INFO | - | Incoming | packet: | {u'count_pir': | 5 | u'lidar_range': | 519 | u'of_dy': | 0 | u'count_uvd': | 109 | u'of_dx': | 0 | u'uvd_range': | 485 | u'count_of': | 0 | u'count_lidar': | 18 | u'version': | 4 | u'of_status': | FALSE | u'pir_status': | FALSE | u'id': | u'trafficCount' | u'of_connected': | TRUE
2015-06-02 | 16:25:57 | 900 | - | INFO | - | Incoming | packet: | {u'count_pir': | 5 | u'lidar_range': | 384 | u'of_dy': | 0 | u'count_uvd': | 109 | u'of_dx': | 0 | u'uvd_range': | 622 | u'count_of': | 0 | u'count_lidar': | 19 | u'version': | 4 | u'of_status': | FALSE | u'pir_status': | FALSE | u'id': | u'trafficCount' | u'of_connected': | TRUE
2015-06-02 | 16:26:04 | 104 | - | INFO | - | Incoming | packet: | {u'count_pir': | 5 | u'lidar_range': | 519 | u'of_dy': | 0 | u'count_uvd': | 110 | u'of_dx': | 0 | u'uvd_range': | 464 | u'count_of': | 0 | u'count_lidar': | 19 | u'version': | 4 | u'of_status': | FALSE | u'pir_status': | FALSE | u'id': | u'trafficCount' | u'of_connected': | TRUE
2015-06-02 | 16:26:05 | 503 | - | INFO | - | Incoming | packet: | {u'count_pir': | 5 | u'lidar_range': | 517 | u'of_dy': | 0 | u'count_uvd': | 111 | u'of_dx': | 0 | u'uvd_range': | 370 | u'count_of': | 0 | u'count_lidar': | 19 | u'version': | 4 | u'of_status': | FALSE | u'pir_status': | FALSE | u'id': | u'trafficCount' | u'of_connected': | TRUE
2015-06-02 | 16:26:05 | 898 | - | INFO | - | Incoming | packet: | {u'count_pir': | 5 | u'lidar_range': | 379 | u'of_dy': | 0 | u'count_uvd': | 111 | u'of_dx': | 0 | u'uvd_range': | 622 | u'count_of': | 0 | u'count_lidar': | 20 | u'version': | 4 | u'of_status': | FALSE | u'pir_status': | FALSE | u'id': | u'trafficCount' | u'of_connected': | TRUE
2015-06-02 | 16:26:09 | 904 | - | INFO | - | Incoming | packet: | {u'count_pir': | 5 | u'lidar_range': | 368 | u'of_dy': | 0 | u'count_uvd': | 112 | u'of_dx': | 0 | u'uvd_range': | 480 | u'count_of': | 0 | u'count_lidar': | 20 | u'version': | 4 | u'of_status': | FALSE | u'pir_status': | FALSE | u'id': | u'trafficCount' | u'of_connected': | TRUE
2015-06-02 | 16:26:11 | 302 | - | INFO | - | Incoming | packet: | {u'count_pir': | 5 | u'lidar_range': | 362 | u'of_dy': | 0 | u'count_uvd': | 113 | u'of_dx': | 0 | u'uvd_range': | 311 | u'count_of': | 0 | u'count_lidar': | 20 | u'version': | 4 | u'of_status': | FALSE | u'pir_status': | FALSE | u'id': | u'trafficCount' | u'of_connected': | TRUE
2015-06-02 | 16:26:17 | 703 | - | INFO | - | Incoming | packet: | {u'count_pir': | 5 | u'lidar_range': | 519 | u'of_dy': | 0 | u'count_uvd': | 114 | u'of_dx': | 0 | u'uvd_range': | 567 | u'count_of': | 0 | u'count_lidar': | 20 | u'version': | 4 | u'of_status': | FALSE | u'pir_status': | FALSE | u'id': | u'trafficCount' | u'of_connected': | TRUE
2015-06-02 | 16:26:23 | 503 | - | INFO | - | Incoming | packet: | {u'count_pir': | 5 | u'lidar_range': | 517 | u'of_dy': | 0 | u'count_uvd': | 115 | u'of_dx': | 0 | u'uvd_range': | 555 | u'count_of': | 0 | u'count_lidar': | 20 | u'version': | 4 | u'of_status': | FALSE | u'pir_status': | FALSE | u'id': | u'trafficCount' | u'of_connected': | TRUE
2015-06-02 | 16:26:24 | 102 | - | INFO | - | Incoming | packet: | {u'count_pir': | 5 | u'lidar_range': | 519 | u'of_dy': | 0 | u'count_uvd': | 116 | u'of_dx': | 0 | u'uvd_range': | 531 | u'count_of': | 0 | u'count_lidar': | 20 | u'version': | 4 | u'of_status': | FALSE | u'pir_status': | FALSE | u'id': | u'trafficCount' | u'of_connected': | TRUE
2015-06-02 | 16:26:26 | 302 | - | INFO | - | Incoming | packet: | {u'count_pir': | 5 | u'lidar_range': | 452 | u'of_dy': | 0 | u'count_uvd': | 116 | u'of_dx': | 0 | u'uvd_range': | 622 | u'count_of': | 0 | u'count_lidar': | 21 | u'version': | 4 | u'of_status': | FALSE | u'pir_status': | FALSE | u'id': | u'trafficCount' | u'of_connected': | TRUE
2015-06-02 | 16:26:35 | 102 | - | INFO | - | Incoming | packet: | {u'count_pir': | 5 | u'lidar_range': | 521 | u'of_dy': | 0 | u'count_uvd': | 117 | u'of_dx': | 0 | u'uvd_range': | 519 | u'count_of': | 0 | u'count_lidar': | 21 | u'version': | 4 | u'of_status': | FALSE | u'pir_status': | FALSE | u'id': | u'trafficCount' | u'of_connected': | TRUE
2015-06-02 | 16:26:38 | 505 | - | INFO | - | Incoming | packet: | {u'count_pir': | 5 | u'lidar_range': | 516 | u'of_dy': | 0 | u'count_uvd': | 118 | u'of_dx': | 0 | u'uvd_range': | 399 | u'count_of': | 0 | u'count_lidar': | 21 | u'version': | 4 | u'of_status': | FALSE | u'pir_status': | FALSE | u'id': | u'trafficCount' | u'of_connected': | TRUE
2015-06-02 | 16:26:41 | 98 | - | INFO | - | Incoming | packet: | {u'count_pir': | 5 | u'lidar_range': | 408 | u'of_dy': | 0 | u'count_uvd': | 118 | u'of_dx': | 0 | u'uvd_range': | 622 | u'count_of': | 0 | u'count_lidar': | 22 | u'version': | 4 | u'of_status': | FALSE | u'pir_status': | FALSE | u'id': | u'trafficCount' | u'of_connected': | TRUE
2015-06-02 | 16:26:45 | 703 | - | INFO | - | Incoming | packet: | {u'count_pir': | 5 | u'lidar_range': | 515 | u'of_dy': | 0 | u'count_uvd': | 119 | u'of_dx': | 0 | u'uvd_range': | 282 | u'count_of': | 0 | u'count_lidar': | 22 | u'version': | 4 | u'of_status': | FALSE | u'pir_status': | FALSE | u'id': | u'trafficCount' | u'of_connected': | TRUE
2015-06-02 | 16:26:47 | 703 | - | INFO | - | Incoming | packet: | {u'count_pir': | 5 | u'lidar_range': | 516 | u'of_dy': | 0 | u'count_uvd': | 120 | u'of_dx': | 0 | u'uvd_range': | 496 | u'count_of': | 0 | u'count_lidar': | 22 | u'version': | 4 | u'of_status': | FALSE | u'pir_status': | FALSE | u'id': | u'trafficCount' | u'of_connected': | TRUE
2015-06-02 | 16:26:53 | 904 | - | INFO | - | Incoming | packet: | {u'count_pir': | 5 | u'lidar_range': | 517 | u'of_dy': | 0 | u'count_uvd': | 121 | u'of_dx': | 0 | u'uvd_range': | 346 | u'count_of': | 0 | u'count_lidar': | 22 | u'version': | 4 | u'of_status': | FALSE | u'pir_status': | FALSE | u'id': | u'trafficCount' | u'of_connected': | TRUE
2015-06-02 | 16:27:09 | 503 | - | INFO | - | Incoming | packet: | {u'count_pir': | 5 | u'lidar_range': | 519 | u'of_dy': | 0 | u'count_uvd': | 122 | u'of_dx': | 0 | u'uvd_range': | 547 | u'count_of': | 0 | u'count_lidar': | 22 | u'version': | 4 | u'of_status': | FALSE | u'pir_status': | FALSE | u'id': | u'trafficCount' | u'of_connected': | TRUE
2015-06-02 | 16:27:13 | 900 | - | INFO | - | Incoming | packet: | {u'count_pir': | 5 | u'lidar_range': | 440 | u'of_dy': | 0 | u'count_uvd': | 122 | u'of_dx': | 0 | u'uvd_range': | 622 | u'count_of': | 0 | u'count_lidar': | 23 | u'version': | 4 | u'of_status': | FALSE | u'pir_status': | FALSE | u'id': | u'trafficCount' | u'of_connected': | TRUE
2015-06-02 | 16:27:14 | 101 | - | INFO | - | Incoming | packet: | {u'count_pir': | 5 | u'lidar_range': | 376 | u'of_dy': | 0 | u'count_uvd': | 122 | u'of_dx': | 0 | u'uvd_range': | 620 | u'count_of': | 0 | u'count_lidar': | 24 | u'version': | 4 | u'of_status': | FALSE | u'pir_status': | FALSE | u'id': | u'trafficCount' | u'of_connected': | TRUE
2015-06-02 | 16:27:23 | 904 | - | INFO | - | Incoming | packet: | {u'count_pir': | 5 | u'lidar_range': | 521 | u'of_dy': | 0 | u'count_uvd': | 123 | u'of_dx': | 0 | u'uvd_range': | 296 | u'count_of': | 0 | u'count_lidar': | 24 | u'version': | 4 | u'of_status': | FALSE | u'pir_status': | FALSE | u'id': | u'trafficCount' | u'of_connected': | TRUE
2015-06-02 | 16:27:26 | 503 | - | INFO | - | Incoming | packet: | {u'count_pir': | 5 | u'lidar_range': | 519 | u'of_dy': | 0 | u'count_uvd': | 124 | u'of_dx': | 0 | u'uvd_range': | 529 | u'count_of': | 0 | u'count_lidar': | 24 | u'version': | 4 | u'of_status': | FALSE | u'pir_status': | FALSE | u'id': | u'trafficCount' | u'of_connected': | TRUE
2015-06-02 | 16:27:28 | 302 | - | INFO | - | Incoming | packet: | {u'count_pir': | 5 | u'lidar_range': | 517 | u'of_dy': | 0 | u'count_uvd': | 125 | u'of_dx': | 0 | u'uvd_range': | 344 | u'count_of': | 0 | u'count_lidar': | 24 | u'version': | 4 | u'of_status': | FALSE | u'pir_status': | FALSE | u'id': | u'trafficCount' | u'of_connected': | TRUE
2015-06-02 | 16:27:32 | 303 | - | INFO | - | Incoming | packet: | {u'count_pir': | 5 | u'lidar_range': | 516 | u'of_dy': | 0 | u'count_uvd': | 126 | u'of_dx': | 0 | u'uvd_range': | 510 | u'count_of': | 0 | u'count_lidar': | 24 | u'version': | 4 | u'of_status': | FALSE | u'pir_status': | FALSE | u'id': | u'trafficCount' | u'of_connected': | TRUE
2015-06-02 | 16:27:35 | 503 | - | INFO | - | Incoming | packet: | {u'count_pir': | 5 | u'lidar_range': | 520 | u'of_dy': | 0 | u'count_uvd': | 127 | u'of_dx': | 0 | u'uvd_range': | 496 | u'count_of': | 0 | u'count_lidar': | 24 | u'version': | 4 | u'of_status': | FALSE | u'pir_status': | FALSE | u'id': | u'trafficCount' | u'of_connected': | TRUE
2015-06-02 | 16:27:38 | 104 | - | INFO | - | Incoming | packet: | {u'count_pir': | 5 | u'lidar_range': | 515 | u'of_dy': | 0 | u'count_uvd': | 128 | u'of_dx': | 0 | u'uvd_range': | 416 | u'count_of': | 0 | u'count_lidar': | 24 | u'version': | 4 | u'of_status': | FALSE | u'pir_status': | FALSE | u'id': | u'trafficCount' | u'of_connected': | TRUE
2015-06-02 | 16:27:41 | 302 | - | INFO | - | Incoming | packet: | {u'count_pir': | 5 | u'lidar_range': | 518 | u'of_dy': | 0 | u'count_uvd': | 129 | u'of_dx': | 0 | u'uvd_range': | 393 | u'count_of': | 0 | u'count_lidar': | 24 | u'version': | 4 | u'of_status': | FALSE | u'pir_status': | FALSE | u'id': | u'trafficCount' | u'of_connected': | TRUE
2015-06-02 | 16:27:41 | 903 | - | INFO | - | Incoming | packet: | {u'count_pir': | 5 | u'lidar_range': | 517 | u'of_dy': | 0 | u'count_uvd': | 130 | u'of_dx': | 0 | u'uvd_range': | 377 | u'count_of': | 0 | u'count_lidar': | 24 | u'version': | 4 | u'of_status': | FALSE | u'pir_status': | FALSE | u'id': | u'trafficCount' | u'of_connected': | TRUE
2015-06-02 | 16:27:43 | 903 | - | INFO | - | Incoming | packet: | {u'count_pir': | 5 | u'lidar_range': | 520 | u'of_dy': | 0 | u'count_uvd': | 131 | u'of_dx': | 0 | u'uvd_range': | 322 | u'count_of': | 0 | u'count_lidar': | 24 | u'version': | 4 | u'of_status': | FALSE | u'pir_status': | FALSE | u'id': | u'trafficCount' | u'of_connected': | TRUE
2015-06-02 | 16:27:47 | 701 | - | INFO | - | Incoming | packet: | {u'count_pir': | 5 | u'lidar_range': | 519 | u'of_dy': | 0 | u'count_uvd': | 132 | u'of_dx': | 0 | u'uvd_range': | 317 | u'count_of': | 0 | u'count_lidar': | 24 | u'version': | 4 | u'of_status': | FALSE | u'pir_status': | FALSE | u'id': | u'trafficCount' | u'of_connected': | TRUE
2015-06-02 | 16:27:53 | 503 | - | INFO | - | Incoming | packet: | {u'count_pir': | 5 | u'lidar_range': | 515 | u'of_dy': | 0 | u'count_uvd': | 133 | u'of_dx': | 0 | u'uvd_range': | 352 | u'count_of': | 0 | u'count_lidar': | 24 | u'version': | 4 | u'of_status': | FALSE | u'pir_status': | FALSE | u'id': | u'trafficCount' | u'of_connected': | TRUE
2015-06-02 | 16:27:55 | 101 | - | INFO | - | Incoming | packet: | {u'count_pir': | 5 | u'lidar_range': | 520 | u'of_dy': | 0 | u'count_uvd': | 134 | u'of_dx': | 0 | u'uvd_range': | 406 | u'count_of': | 0 | u'count_lidar': | 24 | u'version': | 4 | u'of_status': | FALSE | u'pir_status': | FALSE | u'id': | u'trafficCount' | u'of_connected': | TRUE
2015-06-02 | 16:27:57 | 503 | - | INFO | - | Incoming | packet: | {u'count_pir': | 5 | u'lidar_range': | 516 | u'of_dy': | 0 | u'count_uvd': | 135 | u'of_dx': | 0 | u'uvd_range': | 497 | u'count_of': | 0 | u'count_lidar': | 24 | u'version': | 4 | u'of_status': | FALSE | u'pir_status': | FALSE | u'id': | u'trafficCount' | u'of_connected': | TRUE
2015-06-02 | 16:28:05 | 703 | - | INFO | - | Incoming | packet: | {u'count_pir': | 5 | u'lidar_range': | 517 | u'of_dy': | 0 | u'count_uvd': | 136 | u'of_dx': | 0 | u'uvd_range': | 565 | u'count_of': | 0 | u'count_lidar': | 24 | u'version': | 4 | u'of_status': | FALSE | u'pir_status': | FALSE | u'id': | u'trafficCount' | u'of_connected': | TRUE
2015-06-02 | 16:28:07 | 102 | - | INFO | - | Incoming | packet: | {u'count_pir': | 5 | u'lidar_range': | 517 | u'of_dy': | 0 | u'count_uvd': | 137 | u'of_dx': | 0 | u'uvd_range': | 481 | u'count_of': | 0 | u'count_lidar': | 24 | u'version': | 4 | u'of_status': | FALSE | u'pir_status': | FALSE | u'id': | u'trafficCount' | u'of_connected': | TRUE
2015-06-02 | 16:28:12 | 500 | - | INFO | - | Incoming | packet: | {u'count_pir': | 5 | u'lidar_range': | 406 | u'of_dy': | 0 | u'count_uvd': | 137 | u'of_dx': | 0 | u'uvd_range': | 621 | u'count_of': | 0 | u'count_lidar': | 25 | u'version': | 4 | u'of_status': | FALSE | u'pir_status': | FALSE | u'id': | u'trafficCount' | u'of_connected': | TRUE
2015-06-02 | 16:28:12 | 901 | - | INFO | - | Incoming | packet: | {u'count_pir': | 5 | u'lidar_range': | 489 | u'of_dy': | 0 | u'count_uvd': | 138 | u'of_dx': | 0 | u'uvd_range': | 457 | u'count_of': | 0 | u'count_lidar': | 25 | u'version': | 4 | u'of_status': | FALSE | u'pir_status': | FALSE | u'id': | u'trafficCount' | u'of_connected': | TRUE
2015-06-02 | 16:28:28 | 500 | - | INFO | - | Incoming | packet: | {u'count_pir': | 5 | u'lidar_range': | 518 | u'of_dy': | 0 | u'count_uvd': | 139 | u'of_dx': | 0 | u'uvd_range': | 446 | u'count_of': | 0 | u'count_lidar': | 25 | u'version': | 4 | u'of_status': | FALSE | u'pir_status': | FALSE | u'id': | u'trafficCount' | u'of_connected': | TRUE
2015-06-02 | 16:28:32 | 301 | - | INFO | - | Incoming | packet: | {u'count_pir': | 5 | u'lidar_range': | 517 | u'of_dy': | 0 | u'count_uvd': | 140 | u'of_dx': | 0 | u'uvd_range': | 307 | u'count_of': | 0 | u'count_lidar': | 25 | u'version': | 4 | u'of_status': | FALSE | u'pir_status': | FALSE | u'id': | u'trafficCount' | u'of_connected': | TRUE
2015-06-02 | 16:28:34 | 303 | - | INFO | - | Incoming | packet: | {u'count_pir': | 5 | u'lidar_range': | 516 | u'of_dy': | 0 | u'count_uvd': | 141 | u'of_dx': | 0 | u'uvd_range': | 398 | u'count_of': | 0 | u'count_lidar': | 25 | u'version': | 4 | u'of_status': | FALSE | u'pir_status': | FALSE | u'id': | u'trafficCount' | u'of_connected': | TRUE
2015-06-02 | 16:28:38 | 302 | - | INFO | - | Incoming | packet: | {u'count_pir': | 5 | u'lidar_range': | 519 | u'of_dy': | 0 | u'count_uvd': | 142 | u'of_dx': | 0 | u'uvd_range': | 557 | u'count_of': | 0 | u'count_lidar': | 25 | u'version': | 4 | u'of_status': | FALSE | u'pir_status': | FALSE | u'id': | u'trafficCount' | u'of_connected': | TRUE
2015-06-02 | 16:28:40 | 102 | - | INFO | - | Incoming | packet: | {u'count_pir': | 5 | u'lidar_range': | 518 | u'of_dy': | 0 | u'count_uvd': | 143 | u'of_dx': | 0 | u'uvd_range': | 395 | u'count_of': | 0 | u'count_lidar': | 25 | u'version': | 4 | u'of_status': | FALSE | u'pir_status': | FALSE | u'id': | u'trafficCount' | u'of_connected': | TRUE
2015-06-02 | 16:28:43 | 98 | - | INFO | - | Incoming | packet: | {u'count_pir': | 5 | u'lidar_range': | 421 | u'of_dy': | 0 | u'count_uvd': | 143 | u'of_dx': | 0 | u'uvd_range': | 621 | u'count_of': | 0 | u'count_lidar': | 26 | u'version': | 4 | u'of_status': | FALSE | u'pir_status': | FALSE | u'id': | u'trafficCount' | u'of_connected': | TRUE
2015-06-02 | 16:28:43 | 302 | - | INFO | - | Incoming | packet: | {u'count_pir': | 5 | u'lidar_range': | 420 | u'of_dy': | 0 | u'count_uvd': | 144 | u'of_dx': | 0 | u'uvd_range': | 310 | u'count_of': | 0 | u'count_lidar': | 26 | u'version': | 4 | u'of_status': | FALSE | u'pir_status': | FALSE | u'id': | u'trafficCount' | u'of_connected': | TRUE
2015-06-02 | 16:28:44 | 104 | - | INFO | - | Incoming | packet: | {u'count_pir': | 5 | u'lidar_range': | 416 | u'of_dy': | 0 | u'count_uvd': | 145 | u'of_dx': | 0 | u'uvd_range': | 534 | u'count_of': | 0 | u'count_lidar': | 26 | u'version': | 4 | u'of_status': | FALSE | u'pir_status': | FALSE | u'id': | u'trafficCount' | u'of_connected': | TRUE
2015-06-02 | 16:28:53 | 104 | - | INFO | - | Incoming | packet: | {u'count_pir': | 5 | u'lidar_range': | 519 | u'of_dy': | 0 | u'count_uvd': | 146 | u'of_dx': | 0 | u'uvd_range': | 555 | u'count_of': | 0 | u'count_lidar': | 26 | u'version': | 4 | u'of_status': | FALSE | u'pir_status': | FALSE | u'id': | u'trafficCount' | u'of_connected': | TRUE
2015-06-02 | 16:28:57 | 101 | - | INFO | - | Incoming | packet: | {u'count_pir': | 5 | u'lidar_range': | 516 | u'of_dy': | 0 | u'count_uvd': | 147 | u'of_dx': | 0 | u'uvd_range': | 365 | u'count_of': | 0 | u'count_lidar': | 26 | u'version': | 4 | u'of_status': | FALSE | u'pir_status': | FALSE | u'id': | u'trafficCount' | u'of_connected': | TRUE
2015-06-02 | 16:28:57 | 700 | - | INFO | - | Incoming | packet: | {u'count_pir': | 5 | u'lidar_range': | 456 | u'of_dy': | 0 | u'count_uvd': | 147 | u'of_dx': | 0 | u'uvd_range': | 621 | u'count_of': | 0 | u'count_lidar': | 27 | u'version': | 4 | u'of_status': | FALSE | u'pir_status': | FALSE | u'id': | u'trafficCount' | u'of_connected': | TRUE
2015-06-02 | 16:28:59 | 497 | - | INFO | - | Incoming | packet: | {u'count_pir': | 5 | u'lidar_range': | 358 | u'of_dy': | 0 | u'count_uvd': | 147 | u'of_dx': | 0 | u'uvd_range': | 621 | u'count_of': | 0 | u'count_lidar': | 28 | u'version': | 4 | u'of_status': | FALSE | u'pir_status': | FALSE | u'id': | u'trafficCount' | u'of_connected': | TRUE
2015-06-02 | 16:29:00 | 901 | - | INFO | - | Incoming | packet: | {u'count_pir': | 5 | u'lidar_range': | 410 | u'of_dy': | 0 | u'count_uvd': | 147 | u'of_dx': | 0 | u'uvd_range': | 621 | u'count_of': | 0 | u'count_lidar': | 29 | u'version': | 4 | u'of_status': | FALSE | u'pir_status': | FALSE | u'id': | u'trafficCount' | u'of_connected': | TRUE
2015-06-02 | 16:29:02 | 901 | - | INFO | - | Incoming | packet: | {u'count_pir': | 5 | u'lidar_range': | 465 | u'of_dy': | 0 | u'count_uvd': | 148 | u'of_dx': | 0 | u'uvd_range': | 377 | u'count_of': | 0 | u'count_lidar': | 29 | u'version': | 4 | u'of_status': | FALSE | u'pir_status': | FALSE | u'id': | u'trafficCount' | u'of_connected': | TRUE
2015-06-02 | 16:29:05 | 302 | - | INFO | - | Incoming | packet: | {u'count_pir': | 5 | u'lidar_range': | 465 | u'of_dy': | 0 | u'count_uvd': | 149 | u'of_dx': | 0 | u'uvd_range': | 542 | u'count_of': | 0 | u'count_lidar': | 29 | u'version': | 4 | u'of_status': | FALSE | u'pir_status': | FALSE | u'id': | u'trafficCount' | u'of_connected': | TRUE
2015-06-02 | 16:29:06 | 502 | - | INFO | - | Incoming | packet: | {u'count_pir': | 5 | u'lidar_range': | 517 | u'of_dy': | 0 | u'count_uvd': | 150 | u'of_dx': | 0 | u'uvd_range': | 546 | u'count_of': | 0 | u'count_lidar': | 29 | u'version': | 4 | u'of_status': | FALSE | u'pir_status': | FALSE | u'id': | u'trafficCount' | u'of_connected': | TRUE
2015-06-02 | 16:29:06 | 901 | - | INFO | - | Incoming | packet: | {u'count_pir': | 5 | u'lidar_range': | 519 | u'of_dy': | 0 | u'count_uvd': | 151 | u'of_dx': | 0 | u'uvd_range': | 563 | u'count_of': | 0 | u'count_lidar': | 29 | u'version': | 4 | u'of_status': | FALSE | u'pir_status': | FALSE | u'id': | u'trafficCount' | u'of_connected': | TRUE
2015-06-02 | 16:29:08 | 701 | - | INFO | - | Incoming | packet: | {u'count_pir': | 5 | u'lidar_range': | 520 | u'of_dy': | 0 | u'count_uvd': | 152 | u'of_dx': | 0 | u'uvd_range': | 372 | u'count_of': | 0 | u'count_lidar': | 29 | u'version': | 4 | u'of_status': | FALSE | u'pir_status': | FALSE | u'id': | u'trafficCount' | u'of_connected': | TRUE
2015-06-02 | 16:29:12 | 502 | - | INFO | - | Incoming | packet: | {u'count_pir': | 5 | u'lidar_range': | 519 | u'of_dy': | 0 | u'count_uvd': | 153 | u'of_dx': | 0 | u'uvd_range': | 554 | u'count_of': | 0 | u'count_lidar': | 29 | u'version': | 4 | u'of_status': | FALSE | u'pir_status': | FALSE | u'id': | u'trafficCount' | u'of_connected': | TRUE
2015-06-02 | 16:29:14 | 500 | - | INFO | - | Incoming | packet: | {u'count_pir': | 5 | u'lidar_range': | 518 | u'of_dy': | 0 | u'count_uvd': | 154 | u'of_dx': | 0 | u'uvd_range': | 359 | u'count_of': | 0 | u'count_lidar': | 29 | u'version': | 4 | u'of_status': | FALSE | u'pir_status': | FALSE | u'id': | u'trafficCount' | u'of_connected': | TRUE
2015-06-02 | 16:29:18 | 302 | - | INFO | - | Incoming | packet: | {u'count_pir': | 5 | u'lidar_range': | 521 | u'of_dy': | 0 | u'count_uvd': | 155 | u'of_dx': | 0 | u'uvd_range': | 311 | u'count_of': | 0 | u'count_lidar': | 29 | u'version': | 4 | u'of_status': | FALSE | u'pir_status': | FALSE | u'id': | u'trafficCount' | u'of_connected': | TRUE
2015-06-02 | 16:29:19 | 101 | - | INFO | - | Incoming | packet: | {u'count_pir': | 5 | u'lidar_range': | 520 | u'of_dy': | 0 | u'count_uvd': | 156 | u'of_dx': | 0 | u'uvd_range': | 520 | u'count_of': | 0 | u'count_lidar': | 29 | u'version': | 4 | u'of_status': | FALSE | u'pir_status': | FALSE | u'id': | u'trafficCount' | u'of_connected': | TRUE
2015-06-02 | 16:29:20 | 901 | - | INFO | - | Incoming | packet: | {u'count_pir': | 5 | u'lidar_range': | 517 | u'of_dy': | 0 | u'count_uvd': | 157 | u'of_dx': | 0 | u'uvd_range': | 522 | u'count_of': | 0 | u'count_lidar': | 29 | u'version': | 4 | u'of_status': | FALSE | u'pir_status': | FALSE | u'id': | u'trafficCount' | u'of_connected': | TRUE
2015-06-02 | 16:29:30 | 102 | - | INFO | - | Incoming | packet: | {u'count_pir': | 5 | u'lidar_range': | 519 | u'of_dy': | 0 | u'count_uvd': | 158 | u'of_dx': | 0 | u'uvd_range': | 454 | u'count_of': | 0 | u'count_lidar': | 29 | u'version': | 4 | u'of_status': | FALSE | u'pir_status': | FALSE | u'id': | u'trafficCount' | u'of_connected': | TRUE
2015-06-02 | 16:29:30 | 502 | - | INFO | - | Incoming | packet: | {u'count_pir': | 5 | u'lidar_range': | 519 | u'of_dy': | 0 | u'count_uvd': | 159 | u'of_dx': | 0 | u'uvd_range': | 511 | u'count_of': | 0 | u'count_lidar': | 29 | u'version': | 4 | u'of_status': | FALSE | u'pir_status': | FALSE | u'id': | u'trafficCount' | u'of_connected': | TRUE
2015-06-02 | 16:29:43 | 701 | - | INFO | - | Incoming | packet: | {u'count_pir': | 5 | u'lidar_range': | 517 | u'of_dy': | 0 | u'count_uvd': | 160 | u'of_dx': | 0 | u'uvd_range': | 455 | u'count_of': | 0 | u'count_lidar': | 29 | u'version': | 4 | u'of_status': | FALSE | u'pir_status': | FALSE | u'id': | u'trafficCount' | u'of_connected': | TRUE
2015-06-02 | 16:29:51 | 499 | - | INFO | - | Incoming | packet: | {u'count_pir': | 5 | u'lidar_range': | 399 | u'of_dy': | 0 | u'count_uvd': | 160 | u'of_dx': | 0 | u'uvd_range': | 621 | u'count_of': | 0 | u'count_lidar': | 30 | u'version': | 4 | u'of_status': | FALSE | u'pir_status': | FALSE | u'id': | u'trafficCount' | u'of_connected': | TRUE
2015-06-02 | 16:29:53 | 302 | - | INFO | - | Incoming | packet: | {u'count_pir': | 5 | u'lidar_range': | 518 | u'of_dy': | 0 | u'count_uvd': | 161 | u'of_dx': | 0 | u'uvd_range': | 373 | u'count_of': | 0 | u'count_lidar': | 30 | u'version': | 4 | u'of_status': | FALSE | u'pir_status': | FALSE | u'id': | u'trafficCount' | u'of_connected': | TRUE
2015-06-02 | 16:29:56 | 700 | - | INFO | - | Incoming | packet: | {u'count_pir': | 5 | u'lidar_range': | 517 | u'of_dy': | 0 | u'count_uvd': | 162 | u'of_dx': | 0 | u'uvd_range': | 531 | u'count_of': | 0 | u'count_lidar': | 30 | u'version': | 4 | u'of_status': | FALSE | u'pir_status': | FALSE | u'id': | u'trafficCount' | u'of_connected': | TRUE
2015-06-02 | 16:29:57 | 497 | - | INFO | - | Incoming | packet: | {u'count_pir': | 5 | u'lidar_range': | 381 | u'of_dy': | 0 | u'count_uvd': | 162 | u'of_dx': | 0 | u'uvd_range': | 621 | u'count_of': | 0 | u'count_lidar': | 31 | u'version': | 4 | u'of_status': | FALSE | u'pir_status': | FALSE | u'id': | u'trafficCount' | u'of_connected': | TRUE
2015-06-02 | 16:30:05 | 502 | - | INFO | - | Incoming | packet: | {u'count_pir': | 5 | u'lidar_range': | 519 | u'of_dy': | 0 | u'count_uvd': | 163 | u'of_dx': | 0 | u'uvd_range': | 477 | u'count_of': | 0 | u'count_lidar': | 31 | u'version': | 4 | u'of_status': | FALSE | u'pir_status': | FALSE | u'id': | u'trafficCount' | u'of_connected': | TRUE
2015-06-02 | 16:30:08 | 302 | - | INFO | - | Incoming | packet: | {u'count_pir': | 5 | u'lidar_range': | 517 | u'of_dy': | 0 | u'count_uvd': | 164 | u'of_dx': | 0 | u'uvd_range': | 315 | u'count_of': | 0 | u'count_lidar': | 31 | u'version': | 4 | u'of_status': | FALSE | u'pir_status': | FALSE | u'id': | u'trafficCount' | u'of_connected': | TRUE
2015-06-02 | 16:30:14 | 701 | - | INFO | - | Incoming | packet: | {u'count_pir': | 5 | u'lidar_range': | 517 | u'of_dy': | 0 | u'count_uvd': | 165 | u'of_dx': | 0 | u'uvd_range': | 325 | u'count_of': | 0 | u'count_lidar': | 31 | u'version': | 4 | u'of_status': | FALSE | u'pir_status': | FALSE | u'id': | u'trafficCount' | u'of_connected': | TRUE
2015-06-02 | 16:30:18 | 502 | - | INFO | - | Incoming | packet: | {u'count_pir': | 5 | u'lidar_range': | 517 | u'of_dy': | 0 | u'count_uvd': | 166 | u'of_dx': | 0 | u'uvd_range': | 336 | u'count_of': | 0 | u'count_lidar': | 31 | u'version': | 4 | u'of_status': | FALSE | u'pir_status': | FALSE | u'id': | u'trafficCount' | u'of_connected': | TRUE
2015-06-02 | 16:30:25 | 101 | - | INFO | - | Incoming | packet: | {u'count_pir': | 5 | u'lidar_range': | 519 | u'of_dy': | 0 | u'count_uvd': | 167 | u'of_dx': | 0 | u'uvd_range': | 513 | u'count_of': | 0 | u'count_lidar': | 31 | u'version': | 4 | u'of_status': | FALSE | u'pir_status': | FALSE | u'id': | u'trafficCount' | u'of_connected': | TRUE
2015-06-02 | 16:30:33 | 98 | - | INFO | - | Incoming | packet: | {u'count_pir': | 5 | u'lidar_range': | 394 | u'of_dy': | 0 | u'count_uvd': | 167 | u'of_dx': | 0 | u'uvd_range': | 621 | u'count_of': | 0 | u'count_lidar': | 32 | u'version': | 4 | u'of_status': | FALSE | u'pir_status': | FALSE | u'id': | u'trafficCount' | u'of_connected': | TRUE
2015-06-02 | 16:30:34 | 101 | - | INFO | - | Incoming | packet: | {u'count_pir': | 5 | u'lidar_range': | 517 | u'of_dy': | 0 | u'count_uvd': | 168 | u'of_dx': | 0 | u'uvd_range': | 391 | u'count_of': | 0 | u'count_lidar': | 32 | u'version': | 4 | u'of_status': | FALSE | u'pir_status': | FALSE | u'id': | u'trafficCount' | u'of_connected': | TRUE
2015-06-02 | 16:30:39 | 298 | - | INFO | - | Incoming | packet: | {u'count_pir': | 5 | u'lidar_range': | 406 | u'of_dy': | 0 | u'count_uvd': | 168 | u'of_dx': | 0 | u'uvd_range': | 621 | u'count_of': | 0 | u'count_lidar': | 33 | u'version': | 4 | u'of_status': | FALSE | u'pir_status': | FALSE | u'id': | u'trafficCount' | u'of_connected': | TRUE
2015-06-02 | 16:30:39 | 901 | - | INFO | - | Incoming | packet: | {u'count_pir': | 5 | u'lidar_range': | 518 | u'of_dy': | 0 | u'count_uvd': | 169 | u'of_dx': | 0 | u'uvd_range': | 388 | u'count_of': | 0 | u'count_lidar': | 33 | u'version': | 4 | u'of_status': | FALSE | u'pir_status': | FALSE | u'id': | u'trafficCount' | u'of_connected': | TRUE
2015-06-02 | 16:30:49 | 701 | - | INFO | - | Incoming | packet: | {u'count_pir': | 5 | u'lidar_range': | 516 | u'of_dy': | 0 | u'count_uvd': | 170 | u'of_dx': | 0 | u'uvd_range': | 506 | u'count_of': | 0 | u'count_lidar': | 33 | u'version': | 4 | u'of_status': | FALSE | u'pir_status': | FALSE | u'id': | u'trafficCount' | u'of_connected': | TRUE
2015-06-02 | 16:30:51 | 502 | - | INFO | - | Incoming | packet: | {u'count_pir': | 5 | u'lidar_range': | 519 | u'of_dy': | 0 | u'count_uvd': | 171 | u'of_dx': | 0 | u'uvd_range': | 325 | u'count_of': | 0 | u'count_lidar': | 33 | u'version': | 4 | u'of_status': | FALSE | u'pir_status': | FALSE | u'id': | u'trafficCount' | u'of_connected': | TRUE
2015-06-02 | 16:30:53 | 500 | - | INFO | - | Incoming | packet: | {u'count_pir': | 5 | u'lidar_range': | 516 | u'of_dy': | 0 | u'count_uvd': | 172 | u'of_dx': | 0 | u'uvd_range': | 508 | u'count_of': | 0 | u'count_lidar': | 33 | u'version': | 4 | u'of_status': | FALSE | u'pir_status': | FALSE | u'id': | u'trafficCount' | u'of_connected': | TRUE
2015-06-02 | 16:30:55 | 502 | - | INFO | - | Incoming | packet: | {u'count_pir': | 5 | u'lidar_range': | 518 | u'of_dy': | 0 | u'count_uvd': | 173 | u'of_dx': | 0 | u'uvd_range': | 444 | u'count_of': | 0 | u'count_lidar': | 33 | u'version': | 4 | u'of_status': | FALSE | u'pir_status': | FALSE | u'id': | u'trafficCount' | u'of_connected': | TRUE
2015-06-02 | 16:31:10 | 901 | - | INFO | - | Incoming | packet: | {u'count_pir': | 5 | u'lidar_range': | 517 | u'of_dy': | 0 | u'count_uvd': | 174 | u'of_dx': | 0 | u'uvd_range': | 404 | u'count_of': | 0 | u'count_lidar': | 33 | u'version': | 4 | u'of_status': | FALSE | u'pir_status': | FALSE | u'id': | u'trafficCount' | u'of_connected': | TRUE
2015-06-02 | 16:31:18 | 99 | - | INFO | - | Incoming | packet: | {u'count_pir': | 5 | u'lidar_range': | 518 | u'of_dy': | 0 | u'count_uvd': | 175 | u'of_dx': | 0 | u'uvd_range': | 343 | u'count_of': | 0 | u'count_lidar': | 33 | u'version': | 4 | u'of_status': | FALSE | u'pir_status': | FALSE | u'id': | u'trafficCount' | u'of_connected': | TRUE
2015-06-02 | 16:31:20 | 101 | - | INFO | - | Incoming | packet: | {u'count_pir': | 5 | u'lidar_range': | 517 | u'of_dy': | 0 | u'count_uvd': | 176 | u'of_dx': | 0 | u'uvd_range': | 322 | u'count_of': | 0 | u'count_lidar': | 33 | u'version': | 4 | u'of_status': | FALSE | u'pir_status': | FALSE | u'id': | u'trafficCount' | u'of_connected': | TRUE
2015-06-02 | 16:31:24 | 101 | - | INFO | - | Incoming | packet: | {u'count_pir': | 5 | u'lidar_range': | 518 | u'of_dy': | 0 | u'count_uvd': | 177 | u'of_dx': | 0 | u'uvd_range': | 551 | u'count_of': | 0 | u'count_lidar': | 33 | u'version': | 4 | u'of_status': | FALSE | u'pir_status': | FALSE | u'id': | u'trafficCount' | u'of_connected': | TRUE
2015-06-02 | 16:31:25 | 901 | - | INFO | - | Incoming | packet: | {u'count_pir': | 5 | u'lidar_range': | 520 | u'of_dy': | 0 | u'count_uvd': | 178 | u'of_dx': | 0 | u'uvd_range': | 360 | u'count_of': | 0 | u'count_lidar': | 33 | u'version': | 4 | u'of_status': | FALSE | u'pir_status': | FALSE | u'id': | u'trafficCount' | u'of_connected': | TRUE
2015-06-02 | 16:31:27 | 299 | - | INFO | - | Incoming | packet: | {u'count_pir': | 5 | u'lidar_range': | 516 | u'of_dy': | 0 | u'count_uvd': | 179 | u'of_dx': | 0 | u'uvd_range': | 350 | u'count_of': | 0 | u'count_lidar': | 33 | u'version': | 4 | u'of_status': | FALSE | u'pir_status': | FALSE | u'id': | u'trafficCount' | u'of_connected': | TRUE
2015-06-02 | 16:31:27 | 901 | - | INFO | - | Incoming | packet: | {u'count_pir': | 5 | u'lidar_range': | 516 | u'of_dy': | 0 | u'count_uvd': | 180 | u'of_dx': | 0 | u'uvd_range': | 255 | u'count_of': | 0 | u'count_lidar': | 33 | u'version': | 4 | u'of_status': | FALSE | u'pir_status': | FALSE | u'id': | u'trafficCount' | u'of_connected': | TRUE
2015-06-02 | 16:31:29 | 901 | - | INFO | - | Incoming | packet: | {u'count_pir': | 5 | u'lidar_range': | 518 | u'of_dy': | 0 | u'count_uvd': | 181 | u'of_dx': | 0 | u'uvd_range': | 563 | u'count_of': | 0 | u'count_lidar': | 33 | u'version': | 4 | u'of_status': | FALSE | u'pir_status': | FALSE | u'id': | u'trafficCount' | u'of_connected': | TRUE
2015-06-02 | 16:31:39 | 98 | - | INFO | - | Incoming | packet: | {u'count_pir': | 5 | u'lidar_range': | 376 | u'of_dy': | 0 | u'count_uvd': | 181 | u'of_dx': | 0 | u'uvd_range': | 621 | u'count_of': | 0 | u'count_lidar': | 34 | u'version': | 4 | u'of_status': | FALSE | u'pir_status': | FALSE | u'id': | u'trafficCount' | u'of_connected': | TRUE
2015-06-02 | 16:31:42 | 72 | - | INFO | - | Incoming | packet: | {u'count_pir': | 6 | u'lidar_range': | 519 | u'of_dy': | 0 | u'count_uvd': | 181 | u'of_dx': | 0 | u'uvd_range': | 621 | u'count_of': | 0 | u'count_lidar': | 34 | u'version': | 4 | u'of_status': | FALSE | u'pir_status': | FALSE | u'id': | u'trafficCount' | u'of_connected': | TRUE
2015-06-02 | 16:31:45 | 299 | - | INFO | - | Incoming | packet: | {u'count_pir': | 6 | u'lidar_range': | 518 | u'of_dy': | 0 | u'count_uvd': | 182 | u'of_dx': | 0 | u'uvd_range': | 452 | u'count_of': | 0 | u'count_lidar': | 34 | u'version': | 4 | u'of_status': | FALSE | u'pir_status': | TRUE | u'id': | u'trafficCount' | u'of_connected': | TRUE
2015-06-02 | 16:31:58 | 299 | - | INFO | - | Incoming | packet: | {u'count_pir': | 6 | u'lidar_range': | 518 | u'of_dy': | 0 | u'count_uvd': | 183 | u'of_dx': | 0 | u'uvd_range': | 332 | u'count_of': | 0 | u'count_lidar': | 34 | u'version': | 4 | u'of_status': | FALSE | u'pir_status': | FALSE | u'id': | u'trafficCount' | u'of_connected': | TRUE
2015-06-02 | 16:32:02 | 302 | - | INFO | - | Incoming | packet: | {u'count_pir': | 6 | u'lidar_range': | 518 | u'of_dy': | 0 | u'count_uvd': | 184 | u'of_dx': | 0 | u'uvd_range': | 461 | u'count_of': | 0 | u'count_lidar': | 34 | u'version': | 4 | u'of_status': | FALSE | u'pir_status': | FALSE | u'id': | u'trafficCount' | u'of_connected': | TRUE
2015-06-02 | 16:32:04 | 105 | - | INFO | - | Incoming | packet: | {u'count_pir': | 7 | u'lidar_range': | 516 | u'of_dy': | 0 | u'count_uvd': | 184 | u'of_dx': | 0 | u'uvd_range': | 621 | u'count_of': | 0 | u'count_lidar': | 34 | u'version': | 4 | u'of_status': | FALSE | u'pir_status': | FALSE | u'id': | u'trafficCount' | u'of_connected': | TRUE
2015-06-02 | 16:32:09 | 901 | - | INFO | - | Incoming | packet: | {u'count_pir': | 7 | u'lidar_range': | 518 | u'of_dy': | 0 | u'count_uvd': | 185 | u'of_dx': | 0 | u'uvd_range': | 280 | u'count_of': | 0 | u'count_lidar': | 34 | u'version': | 4 | u'of_status': | FALSE | u'pir_status': | TRUE | u'id': | u'trafficCount' | u'of_connected': | TRUE
2015-06-02 | 16:32:19 | 701 | - | INFO | - | Incoming | packet: | {u'count_pir': | 7 | u'lidar_range': | 517 | u'of_dy': | 0 | u'count_uvd': | 186 | u'of_dx': | 0 | u'uvd_range': | 475 | u'count_of': | 0 | u'count_lidar': | 34 | u'version': | 4 | u'of_status': | FALSE | u'pir_status': | FALSE | u'id': | u'trafficCount' | u'of_connected': | TRUE
2015-06-02 | 16:32:21 | 101 | - | INFO | - | Incoming | packet: | {u'count_pir': | 7 | u'lidar_range': | 516 | u'of_dy': | 0 | u'count_uvd': | 187 | u'of_dx': | 0 | u'uvd_range': | 374 | u'count_of': | 0 | u'count_lidar': | 34 | u'version': | 4 | u'of_status': | FALSE | u'pir_status': | FALSE | u'id': | u'trafficCount' | u'of_connected': | TRUE
2015-06-02 | 16:32:23 | 99 | - | INFO | - | Incoming | packet: | {u'count_pir': | 7 | u'lidar_range': | 517 | u'of_dy': | 0 | u'count_uvd': | 188 | u'of_dx': | 0 | u'uvd_range': | 440 | u'count_of': | 0 | u'count_lidar': | 34 | u'version': | 4 | u'of_status': | FALSE | u'pir_status': | FALSE | u'id': | u'trafficCount' | u'of_connected': | TRUE
2015-06-02 | 16:32:23 | 500 | - | INFO | - | Incoming | packet: | {u'count_pir': | 7 | u'lidar_range': | 520 | u'of_dy': | 0 | u'count_uvd': | 189 | u'of_dx': | 0 | u'uvd_range': | 512 | u'count_of': | 0 | u'count_lidar': | 34 | u'version': | 4 | u'of_status': | FALSE | u'pir_status': | FALSE | u'id': | u'trafficCount' | u'of_connected': | TRUE
2015-06-02 | 16:32:28 | 900 | - | INFO | - | Incoming | packet: | {u'count_pir': | 7 | u'lidar_range': | 516 | u'of_dy': | 0 | u'count_uvd': | 190 | u'of_dx': | 0 | u'uvd_range': | 446 | u'count_of': | 0 | u'count_lidar': | 34 | u'version': | 4 | u'of_status': | FALSE | u'pir_status': | FALSE | u'id': | u'trafficCount' | u'of_connected': | TRUE
2015-06-02 | 16:32:33 | 301 | - | INFO | - | Incoming | packet: | {u'count_pir': | 7 | u'lidar_range': | 518 | u'of_dy': | 0 | u'count_uvd': | 191 | u'of_dx': | 0 | u'uvd_range': | 552 | u'count_of': | 0 | u'count_lidar': | 34 | u'version': | 4 | u'of_status': | FALSE | u'pir_status': | FALSE | u'id': | u'trafficCount' | u'of_connected': | TRUE
2015-06-02 | 16:32:35 | 101 | - | INFO | - | Incoming | packet: | {u'count_pir': | 7 | u'lidar_range': | 519 | u'of_dy': | 0 | u'count_uvd': | 192 | u'of_dx': | 0 | u'uvd_range': | 344 | u'count_of': | 0 | u'count_lidar': | 34 | u'version': | 4 | u'of_status': | FALSE | u'pir_status': | FALSE | u'id': | u'trafficCount' | u'of_connected': | TRUE
2015-06-02 | 16:32:54 | 99 | - | INFO | - | Incoming | packet: | {u'count_pir': | 7 | u'lidar_range': | 518 | u'of_dy': | 0 | u'count_uvd': | 193 | u'of_dx': | 0 | u'uvd_range': | 373 | u'count_of': | 0 | u'count_lidar': | 34 | u'version': | 4 | u'of_status': | FALSE | u'pir_status': | FALSE | u'id': | u'trafficCount' | u'of_connected': | TRUE
2015-06-02 | 16:33:09 | 500 | - | INFO | - | Incoming | packet: | {u'count_pir': | 7 | u'lidar_range': | 516 | u'of_dy': | 0 | u'count_uvd': | 194 | u'of_dx': | 0 | u'uvd_range': | 284 | u'count_of': | 0 | u'count_lidar': | 34 | u'version': | 4 | u'of_status': | FALSE | u'pir_status': | FALSE | u'id': | u'trafficCount' | u'of_connected': | TRUE
2015-06-02 | 16:33:13 | 138 | - | INFO | - | Incoming | packet: | {u'count_pir': | 8 | u'lidar_range': | 518 | u'of_dy': | 0 | u'count_uvd': | 194 | u'of_dx': | 0 | u'uvd_range': | 621 | u'count_of': | 0 | u'count_lidar': | 34 | u'version': | 4 | u'of_status': | FALSE | u'pir_status': | FALSE | u'id': | u'trafficCount' | u'of_connected': | TRUE
2015-06-02 | 16:33:15 | 901 | - | INFO | - | Incoming | packet: | {u'count_pir': | 8 | u'lidar_range': | 519 | u'of_dy': | 0 | u'count_uvd': | 195 | u'of_dx': | 0 | u'uvd_range': | 525 | u'count_of': | 0 | u'count_lidar': | 34 | u'version': | 4 | u'of_status': | FALSE | u'pir_status': | TRUE | u'id': | u'trafficCount' | u'of_connected': | TRUE
2015-06-02 | 16:33:19 | 96 | - | INFO | - | Incoming | packet: | {u'count_pir': | 8 | u'lidar_range': | 384 | u'of_dy': | 0 | u'count_uvd': | 195 | u'of_dx': | 0 | u'uvd_range': | 621 | u'count_of': | 0 | u'count_lidar': | 35 | u'version': | 4 | u'of_status': | FALSE | u'pir_status': | TRUE | u'id': | u'trafficCount' | u'of_connected': | TRUE
2015-06-02 | 16:33:22 | 700 | - | INFO | - | Incoming | packet: | {u'count_pir': | 8 | u'lidar_range': | 519 | u'of_dy': | 0 | u'count_uvd': | 196 | u'of_dx': | 0 | u'uvd_range': | 431 | u'count_of': | 0 | u'count_lidar': | 35 | u'version': | 4 | u'of_status': | FALSE | u'pir_status': | FALSE | u'id': | u'trafficCount' | u'of_connected': | TRUE
2015-06-02 | 16:33:25 | 101 | - | INFO | - | Incoming | packet: | {u'count_pir': | 8 | u'lidar_range': | 516 | u'of_dy': | 0 | u'count_uvd': | 197 | u'of_dx': | 0 | u'uvd_range': | 369 | u'count_of': | 0 | u'count_lidar': | 35 | u'version': | 4 | u'of_status': | FALSE | u'pir_status': | FALSE | u'id': | u'trafficCount' | u'of_connected': | TRUE
2015-06-02 | 16:33:35 | 99 | - | INFO | - | Incoming | packet: | {u'count_pir': | 8 | u'lidar_range': | 517 | u'of_dy': | 0 | u'count_uvd': | 198 | u'of_dx': | 0 | u'uvd_range': | 519 | u'count_of': | 0 | u'count_lidar': | 35 | u'version': | 4 | u'of_status': | FALSE | u'pir_status': | FALSE | u'id': | u'trafficCount' | u'of_connected': | TRUE
2015-06-02 | 16:33:38 | 500 | - | INFO | - | Incoming | packet: | {u'count_pir': | 8 | u'lidar_range': | 520 | u'of_dy': | 0 | u'count_uvd': | 199 | u'of_dx': | 0 | u'uvd_range': | 564 | u'count_of': | 0 | u'count_lidar': | 35 | u'version': | 4 | u'of_status': | FALSE | u'pir_status': | FALSE | u'id': | u'trafficCount' | u'of_connected': | TRUE
2015-06-02 | 16:33:40 | 500 | - | INFO | - | Incoming | packet: | {u'count_pir': | 8 | u'lidar_range': | 519 | u'of_dy': | 0 | u'count_uvd': | 200 | u'of_dx': | 0 | u'uvd_range': | 268 | u'count_of': | 0 | u'count_lidar': | 35 | u'version': | 4 | u'of_status': | FALSE | u'pir_status': | FALSE | u'id': | u'trafficCount' | u'of_connected': | TRUE
2015-06-02 | 16:33:44 | 502 | - | INFO | - | Incoming | packet: | {u'count_pir': | 8 | u'lidar_range': | 518 | u'of_dy': | 0 | u'count_uvd': | 201 | u'of_dx': | 0 | u'uvd_range': | 360 | u'count_of': | 0 | u'count_lidar': | 35 | u'version': | 4 | u'of_status': | FALSE | u'pir_status': | FALSE | u'id': | u'trafficCount' | u'of_connected': | TRUE
2015-06-02 | 16:44:51 | 207 | - | INFO | - | Incoming | packet: | {u'count_pir': | 16 | u'lidar_range': | 520 | u'of_dy': | 0 | u'count_uvd': | 319 | u'of_dx': | 0 | u'uvd_range': | 390 | u'count_of': | 0 | u'count_lidar': | 45 | u'version': | 4 | u'of_status': | FALSE | u'pir_status': | FALSE | u'id': | u'trafficCount' | u'of_connected': | TRUE
2015-06-02 | 16:44:59 | 3 | - | INFO | - | Incoming | packet: | {u'count_pir': | 16 | u'lidar_range': | 519 | u'of_dy': | 0 | u'count_uvd': | 320 | u'of_dx': | 0 | u'uvd_range': | 542 | u'count_of': | 0 | u'count_lidar': | 45 | u'version': | 4 | u'of_status': | FALSE | u'pir_status': | FALSE | u'id': | u'trafficCount' | u'of_connected': | TRUE
2015-06-02 | 16:45:01 | 0 | - | INFO | - | Incoming | packet: | {u'count_pir': | 16 | u'lidar_range': | 518 | u'of_dy': | 0 | u'count_uvd': | 321 | u'of_dx': | 0 | u'uvd_range': | 466 | u'count_of': | 0 | u'count_lidar': | 45 | u'version': | 4 | u'of_status': | FALSE | u'pir_status': | FALSE | u'id': | u'trafficCount' | u'of_connected': | TRUE
2015-06-02 | 16:45:06 | 796 | - | INFO | - | Incoming | packet: | {u'count_pir': | 16 | u'lidar_range': | 520 | u'of_dy': | 0 | u'count_uvd': | 322 | u'of_dx': | 0 | u'uvd_range': | 449 | u'count_of': | 0 | u'count_lidar': | 45 | u'version': | 4 | u'of_status': | FALSE | u'pir_status': | FALSE | u'id': | u'trafficCount' | u'of_connected': | TRUE
2015-06-02 | 16:45:08 | 194 | - | INFO | - | Incoming | packet: | {u'count_pir': | 16 | u'lidar_range': | 518 | u'of_dy': | 0 | u'count_uvd': | 323 | u'of_dx': | 0 | u'uvd_range': | 319 | u'count_of': | 0 | u'count_lidar': | 45 | u'version': | 4 | u'of_status': | FALSE | u'pir_status': | FALSE | u'id': | u'trafficCount' | u'of_connected': | TRUE
2015-06-02 | 16:45:10 | 595 | - | INFO | - | Incoming | packet: | {u'count_pir': | 16 | u'lidar_range': | 516 | u'of_dy': | 0 | u'count_uvd': | 324 | u'of_dx': | 0 | u'uvd_range': | 432 | u'count_of': | 0 | u'count_lidar': | 45 | u'version': | 4 | u'of_status': | FALSE | u'pir_status': | FALSE | u'id': | u'trafficCount' | u'of_connected': | TRUE
2015-06-02 | 16:45:29 | 984 | - | INFO | - | Incoming | packet: | {u'count_pir': | 16 | u'lidar_range': | 518 | u'of_dy': | 0 | u'count_uvd': | 325 | u'of_dx': | 0 | u'uvd_range': | 560 | u'count_of': | 0 | u'count_lidar': | 45 | u'version': | 4 | u'of_status': | FALSE | u'pir_status': | FALSE | u'id': | u'trafficCount' | u'of_connected': | TRUE
2015-06-02 | 16:45:31 | 984 | - | INFO | - | Incoming | packet: | {u'count_pir': | 16 | u'lidar_range': | 517 | u'of_dy': | 0 | u'count_uvd': | 326 | u'of_dx': | 0 | u'uvd_range': | 394 | u'count_of': | 0 | u'count_lidar': | 45 | u'version': | 4 | u'of_status': | FALSE | u'pir_status': | FALSE | u'id': | u'trafficCount' | u'of_connected': | TRUE
2015-06-02 | 16:45:36 | 585 | - | INFO | - | Incoming | packet: | {u'count_pir': | 16 | u'lidar_range': | 517 | u'of_dy': | 0 | u'count_uvd': | 327 | u'of_dx': | 0 | u'uvd_range': | 367 | u'count_of': | 0 | u'count_lidar': | 45 | u'version': | 4 | u'of_status': | FALSE | u'pir_status': | FALSE | u'id': | u'trafficCount' | u'of_connected': | TRUE
2015-06-02 | 16:45:47 | 153 | - | INFO | - | Incoming | packet: | {u'count_pir': | 17 | u'lidar_range': | 518 | u'of_dy': | 0 | u'count_uvd': | 327 | u'of_dx': | 0 | u'uvd_range': | 610 | u'count_of': | 0 | u'count_lidar': | 45 | u'version': | 4 | u'of_status': | FALSE | u'pir_status': | FALSE | u'id': | u'trafficCount' | u'of_connected': | TRUE
2015-06-02 | 16:45:47 | 780 | - | INFO | - | Incoming | packet: | {u'count_pir': | 17 | u'lidar_range': | 13 | u'of_dy': | 0 | u'count_uvd': | 327 | u'of_dx': | 0 | u'uvd_range': | 621 | u'count_of': | 0 | u'count_lidar': | 46 | u'version': | 4 | u'of_status': | FALSE | u'pir_status': | TRUE | u'id': | u'trafficCount' | u'of_connected': | TRUE
2015-06-02 | 16:45:47 | 983 | - | INFO | - | Incoming | packet: | {u'count_pir': | 17 | u'lidar_range': | 519 | u'of_dy': | 0 | u'count_uvd': | 328 | u'of_dx': | 0 | u'uvd_range': | 27 | u'count_of': | 0 | u'count_lidar': | 46 | u'version': | 4 | u'of_status': | FALSE | u'pir_status': | TRUE | u'id': | u'trafficCount' | u'of_connected': | TRUE
2015-06-02 | 16:45:48 | 615 | - | INFO | - | Incoming | packet: | {u'count_pir': | 17 | u'lidar_range': | 15 | u'of_dy': | 0 | u'count_uvd': | 328 | u'of_dx': | 0 | u'uvd_range': | 621 | u'count_of': | 0 | u'count_lidar': | 47 | u'version': | 4 | u'of_status': | FALSE | u'pir_status': | TRUE | u'id': | u'trafficCount' | u'of_connected': | TRUE
2015-06-02 | 16:45:48 | 621 | - | INFO | - | Incoming | packet: | {u'count_pir': | 17 | u'lidar_range': | 15 | u'of_dy': | 0 | u'count_uvd': | 329 | u'of_dx': | 0 | u'uvd_range': | 22 | u'count_of': | 0 | u'count_lidar': | 47 | u'version': | 4 | u'of_status': | FALSE | u'pir_status': | TRUE | u'id': | u'trafficCount' | u'of_connected': | TRUE
2015-06-02 | 16:45:54 | 384 | - | INFO | - | Incoming | packet: | {u'count_pir': | 17 | u'lidar_range': | 519 | u'of_dy': | 0 | u'count_uvd': | 330 | u'of_dx': | 0 | u'uvd_range': | 338 | u'count_of': | 0 | u'count_lidar': | 47 | u'version': | 4 | u'of_status': | FALSE | u'pir_status': | FALSE | u'id': | u'trafficCount' | u'of_connected': | TRUE

Sheet: Sheet2
Date | Time | PIR Count | PIR Status | Sonar Count | Sonar Range | Lidar Count | Lidar Range | Flow Count | Flow Connected
2015-06-02 | 16:17:47 | 0 | FALSE | 0 | 621 | 0 | 0 | 0 | FALSE
2015-06-02 | 16:17:56 | 0 | FALSE | 1 | 336 | 0 | 519 | 0 | TRUE
2015-06-02 | 16:17:59 | 0 | FALSE | 2 | 522 | 0 | 518 | 0 | TRUE
2015-06-02 | 16:18:06 | 0 | FALSE | 3 | 427 | 0 | 518 | 0 | TRUE
2015-06-02 | 16:18:12 | 0 | FALSE | 4 | 338 | 0 | 519 | 0 | TRUE
2015-06-02 | 16:18:14 | 0 | FALSE | 5 | 292 | 0 | 517 | 0 | TRUE
2015-06-02 | 16:18:14 | 0 | FALSE | 6 | 553 | 0 | 518 | 0 | TRUE
2015-06-02 | 16:18:16 | 0 | FALSE | 7 | 407 | 0 | 517 | 0 | TRUE
2015-06-02 | 16:18:18 | 0 | FALSE | 8 | 483 | 0 | 516 | 0 | TRUE
2015-06-02 | 16:18:18 | 0 | FALSE | 9 | 500 | 0 | 519 | 0 | TRUE
2015-06-02 | 16:18:24 | 0 | FALSE | 10 | 382 | 0 | 518 | 0 | TRUE
2015-06-02 | 16:18:27 | 0 | FALSE | 10 | 622 | 1 | 5 | 0 | TRUE
2015-06-02 | 16:18:28 | 1 | FALSE | 10 | 622 | 1 | 519 | 0 | TRUE
2015-06-02 | 16:18:30 | 1 | TRUE | 11 | 389 | 1 | 516 | 0 | TRUE
2015-06-02 | 16:18:34 | 1 | TRUE | 12 | 520 | 1 | 517 | 0 | TRUE
2015-06-02 | 16:18:36 | 1 | FALSE | 13 | 536 | 1 | 521 | 0 | TRUE
2015-06-02 | 16:18:38 | 1 | FALSE | 14 | 284 | 1 | 518 | 0 | TRUE
2015-06-02 | 16:18:42 | 1 | FALSE | 15 | 556 | 1 | 518 | 0 | TRUE
2015-06-02 | 16:18:42 | 2 | FALSE | 15 | 622 | 1 | 519 | 0 | TRUE
2015-06-02 | 16:18:53 | 2 | FALSE | 16 | 490 | 1 | 516 | 0 | TRUE
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
2015-06-02 | 16:45:47 | 17 | TRUE | 328 | 27 | 46 | 519 | 0 | TRUE
2015-06-02 | 16:45:48 | 17 | TRUE | 328 | 621 | 47 | 15 | 0 | TRUE
2015-06-02 | 16:45:48 | 17 | TRUE | 329 | 22 | 47 | 15 | 0 | TRUE
2015-06-02 | 16:45:54 | 17 | FALSE | 330 | 338 | 47 | 519 | 0 | TRUE
