karl-mohring/TrafficCounter/Pre-deployment Checks/Wboard/OpticalFlowCalibration/config.h

#include "Arduino.h"

// Comms settings
const long SERIAL_BAUD = 57600;
const int LOGGER_LEVEL = LOG_LEVEL_DEBUG;

// Pin assignments
const byte OF_MOSI = 8;
const byte OF_MISO = 7;
const byte OF_SCLK = 9;
const byte OF_NCS = 41;
